lionsarmor/KeychainKreatures/PCBWay/05_Delivery_and_Testing/Inspection_Reports/README.md

# Save received inspection/test reports here

No test result is prefilled. Retain PCBWay net-test/inspection records and your own dated measurements with board serial numbers. Distinguish factory inspection, bare-board continuity and actual powered functional testing.
