lionsarmor/KeychainKreatures/PCBWay/01_Main_C6/01_Gerber_Upload/README.md

# Upload main C.6 Gerbers

Upload **UPLOAD_MAIN_C6_GERBERS.zip** to the MAIN bare-PCB job.

Quantity 5; 96 × 105 mm; 1.6 mm; **2 copper layers**. Read FABRICATION_REQUIREMENTS.md. Gerbers, outline, separate plated/non-plated drills and IPC netlist are included. Main is THT: omitted empty paste layers are intentional, and no assembly/stencil is requested.

Do not upload the power ZIP here. Confirm actual-size fit sheets and real modules before authorizing fabrication; the shell concept art is not fit evidence.
