lionsarmor/KeychainKreatures/PCBWay/01_Main_C6/02_Drawings_and_Reference/README.md

# Main reference drawings

These assembly, schematic and actual-size fit PDFs help PCBWay review the board and help you check purchased parts. They do **not** request factory assembly.

Print fit sheets at 100% and measure their calibration marks. Front and back illustrations have different viewing conventions. Use pad numbers for polarity, not guessed visual left/right order.
