lionsarmor/KeychainKreatures/PCBWay/01_Main_C6/05_Full_Review_Package/README.md

# Supplemental full main engineering package

Attach FULL_MAIN_C6_REVIEW.zip if the reviewer requests complete supporting CAD, datasheets or static checks. It is the existing issued ZIP, unchanged. For the fabrication upload use the smaller ZIP in ../01_Gerber_Upload instead.
