lionsarmor/KeychainKreatures/PCBWay/02_Power_P4/05_Full_Review_Package/README.md

# Supplemental full power engineering package

Attach FULL_POWER_P4_REVIEW.zip to engineering correspondence. It includes source CAD, datasheets, Gerbers, original BOMs/positions and saved electrical/routing checks. It is the issued ZIP, unchanged.

Upload the smaller Gerber ZIP, BOM and SMT centroid into their respective form fields. Do not treat this supplemental ZIP as another five-board order. Read the separate fabrication requirements before approving production.
