lionsarmor/KeychainKreatures/PCBWay/04_Approval_and_Payment/Receipts_and_Approvals/README.md

# Save approval and purchase records here

Currently empty of approvals/orders. Save final quote, explicit approvals, order IDs and receipts after you personally approve an order. Do not store payment credentials or identity documents. Files placed here are locally ignored by Git except this README.
