lionsarmor/KeychainKreatures/revisions/2026-09-12_current_only/KK_main_module/C5_relayout/manufacturing/DRILL_REPORT.txt

Drill report for KK_main_module.kicad_pcb
Created on 2026-09-11T15:05:44

Copper Layer Stackup:
    =============================================================
    L1 :  F.Cu                      front
    L2 :  B.Cu                      back

Drill file 'KK_main_module-PTH.drl' contains
    plated through holes:
    =============================================================
    T1  0.300mm  0.0118"  (40 holes))
    T2  0.400mm  0.0157"  (6 holes))
    T3  0.500mm  0.0197"  (3 holes))
    T4  0.750mm  0.0295"  (4 holes))
    T5  0.800mm  0.0315"  (201 holes))
    T6  0.900mm  0.0354"  (36 holes))
    T7  0.950mm  0.0374"  (4 holes))
    T8  1.000mm  0.0394"  (54 holes))
    T9  1.050mm  0.0413"  (18 holes))
    T10  1.100mm  0.0433"  (5 holes))

    Total plated holes count 371

Drill file 'KK_main_module-NPTH.drl' contains
    unplated through holes:
    =============================================================
    T1  2.200mm  0.0866"  (4 holes))

    Total unplated holes count 4
