lionsarmor/KeychainKreatures/revisions/2026-09-11_cleanup/KK_power_module/manufacturing/release/KK_power_module_0.2-LR1/drill_report.txt

Drill report for KK_power_module.kicad_pcb
Created on 2026-09-09T22:40:37

Copper Layer Stackup:
    =============================================================
    L1 :  F.Cu                      front
    L2 :  B.Cu                      back

Drill file 'KK_power_module-PTH.drl' contains
    plated through holes:
    =============================================================
    T1  0.300mm  0.0118"  (47 holes))
    T2  0.600mm  0.0236"  (4 holes)  (with 4 slots)
    T3  0.750mm  0.0295"  (4 holes))
    T4  1.000mm  0.0394"  (9 holes))

    Total plated holes count 64

Drill file 'KK_power_module-NPTH.drl' contains
    unplated through holes:
    =============================================================
    T1  0.650mm  0.0256"  (2 holes))
    T2  0.900mm  0.0354"  (2 holes))
    T3  2.200mm  0.0866"  (2 holes))

    Total unplated holes count 6
