lionsarmor/KeychainKreatures/revisions/2026-09-12_current_only/KK_main_module/mechanical/fit-study.pdf

# RODDY.WORLD / KEYCHAIN KREATURES

### FIT STUDY · 2026-09-10 · NOT A FABRICATION DRAWING

Print at 100% / actual size. Disable “fit to page”. Confirm the 20 mm calibration line below.

### FRONT · 1:1

62 mm · ring excluded

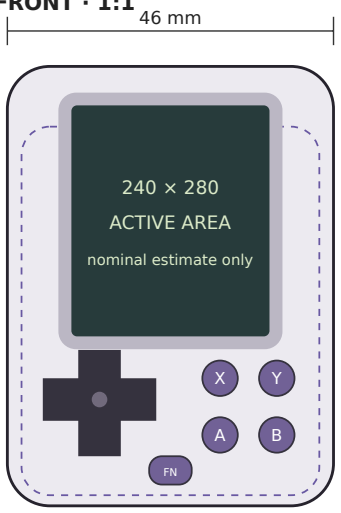
[picture p3: figure]
ACTIVE AREA; nominal estimate only
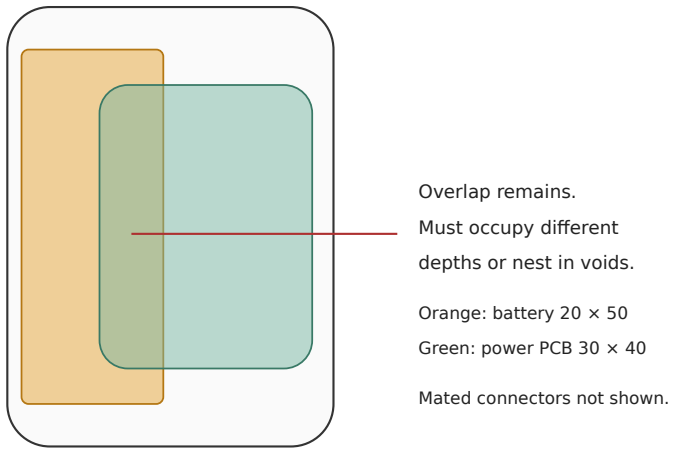
[picture p4: figure]
Overlap remains.; Must occupy different; depths or nest in voids.; Orange: battery 20 × 50; Green: power PCB 30 × 40; Mated connectors not shown.

Dashed: trial 42 × 52 mm PCB, R4. Caps/bezel/PCB position are illustrative. Glass, flex, bosses and travel NOT fitted.

### 19 mm DEPTH BUDGET · 4:1 diagram

Arithmetic lower bound at a four-assembly overlap.

10 mm cell

Gray: two 1.2 mm trial face skins = 2.4 mm

Green: two 1.6 mm PCB laminates = 3.2 mm

Red: ONLY 3.4 mm left for everything else

Display, parts, solder, insulation and gaps omitted.

This is not a physical layer-order drawing.

### OFFSET PLAN · 1:1 envelopes, NOT fitted

20 mm calibration

No screen reduction or housing growth approved.
