lionsarmor/KeychainKreatures/docs/enclosure_concepts/pixel_pod_round2/05_pixel_pod_snap_skins.png

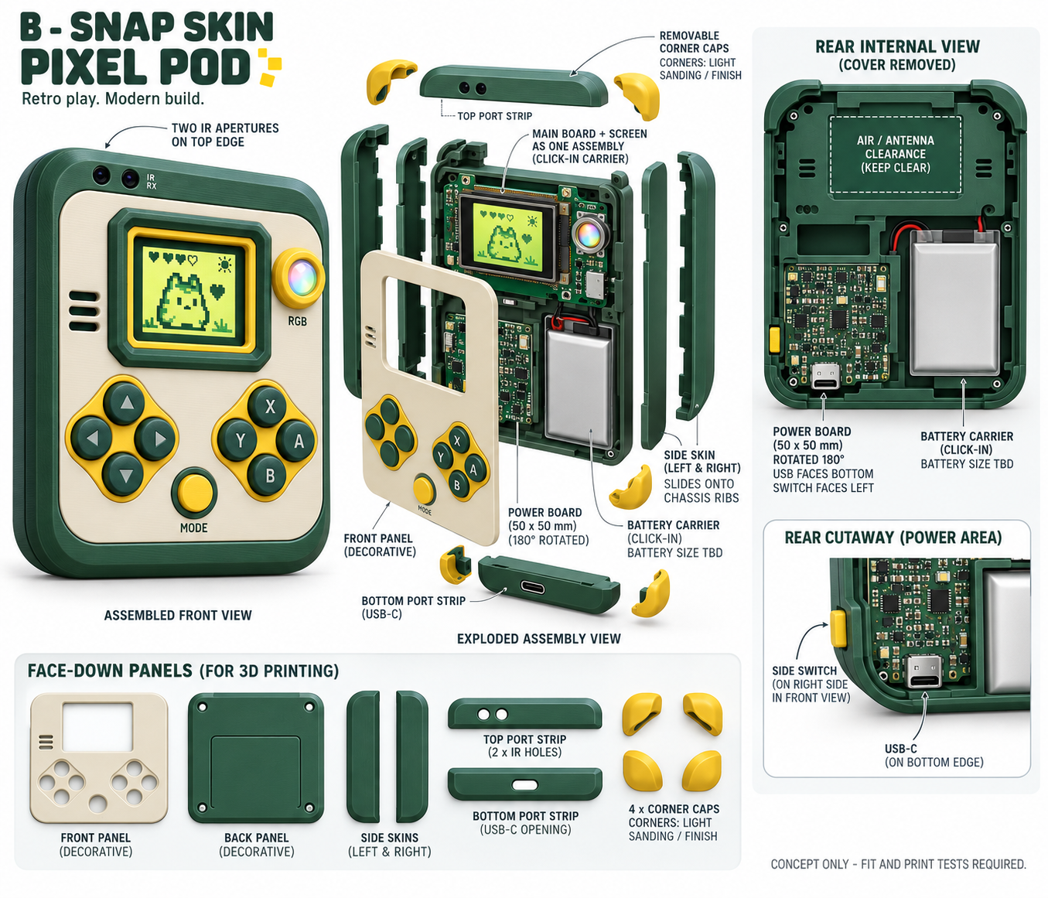
docs/enclosure_concepts/pixel_pod_round2/05_pixel_pod_snap_skins.png
