lionsarmor/KeychainKreatures/KK_main_module/datasheets/soft-buttons.png

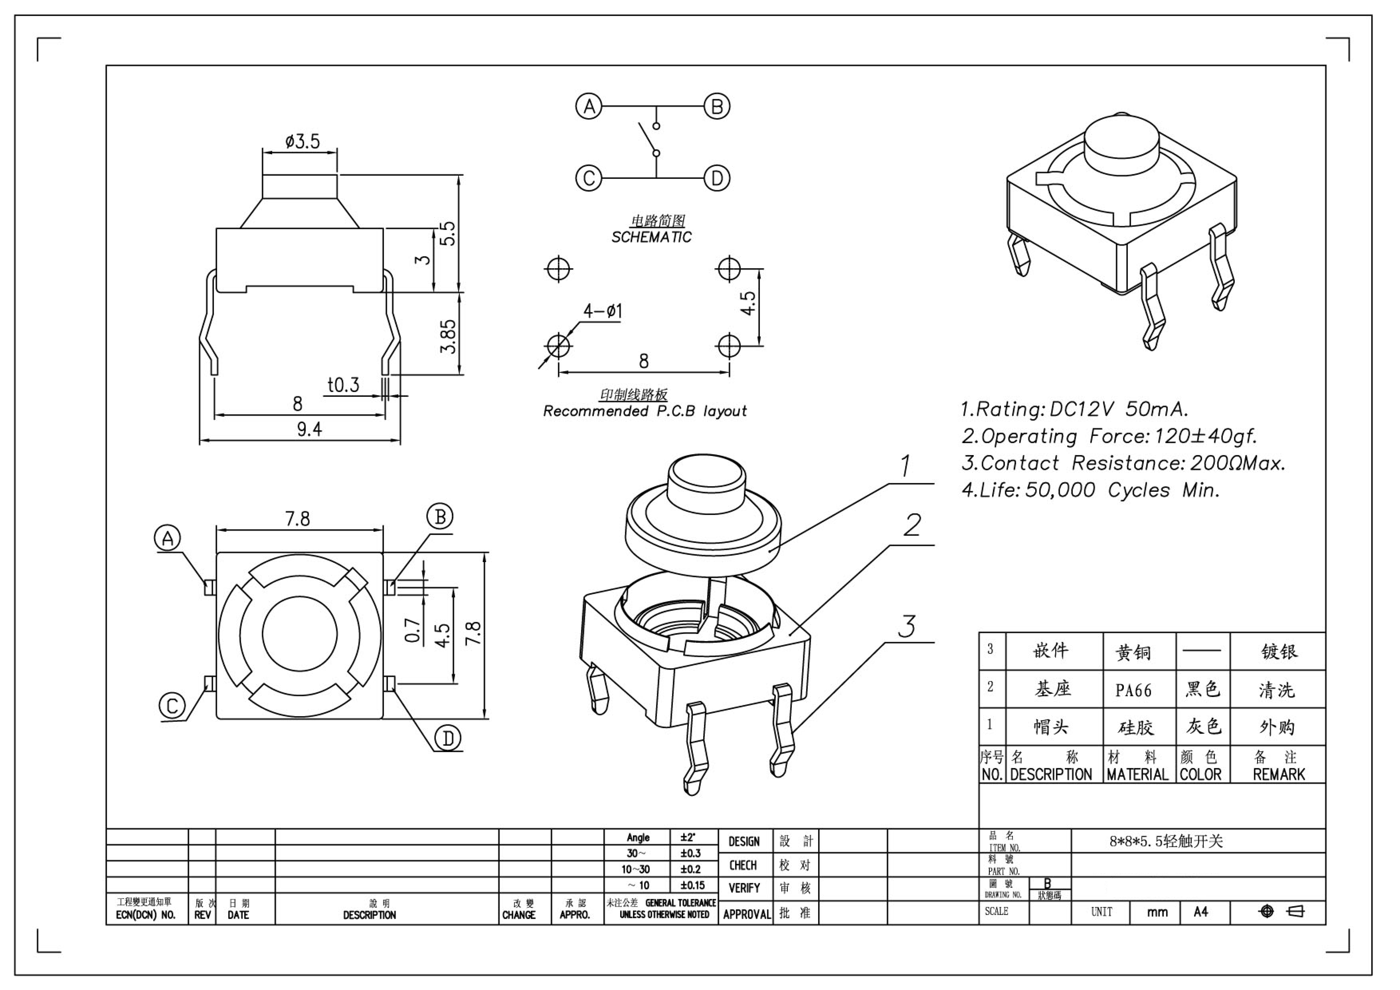
KK_main_module/datasheets/soft-buttons.png
