lionsarmor/KeychainKreatures/KK_power_module/datasheets/FS8205-pinout.png

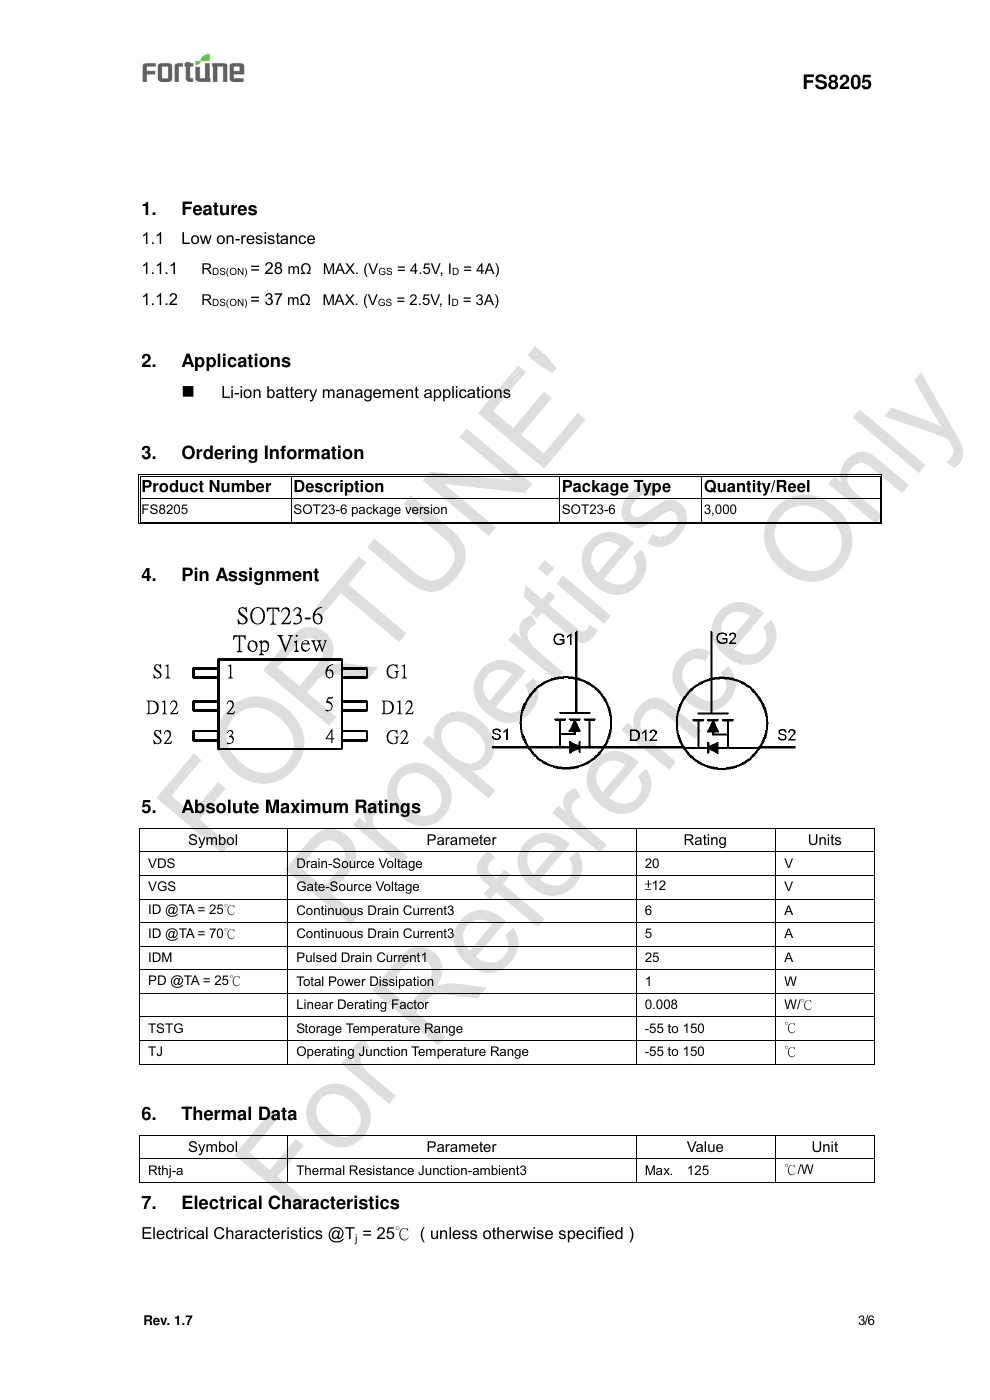
KK_power_module/datasheets/FS8205-pinout.png
