lionsarmor/KeychainKreatures/KK_power_module/datasheets/JST_VH-header.png

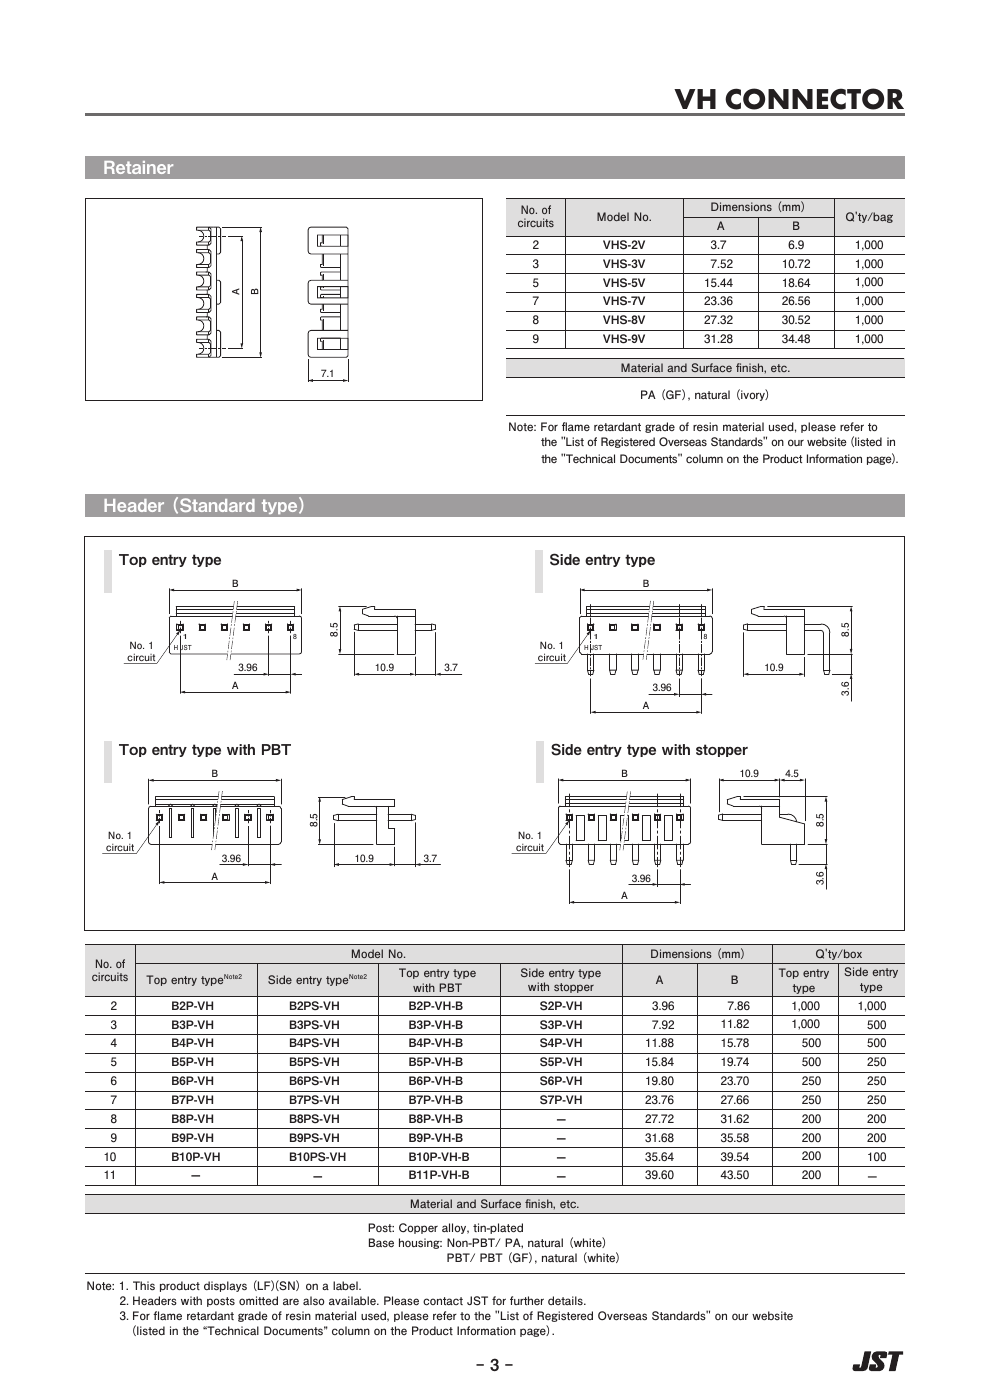
KK_power_module/datasheets/JST_VH-header.png
