lionsarmor/KeychainKreatures/KK_power_module/datasheets/USB-drawing.png

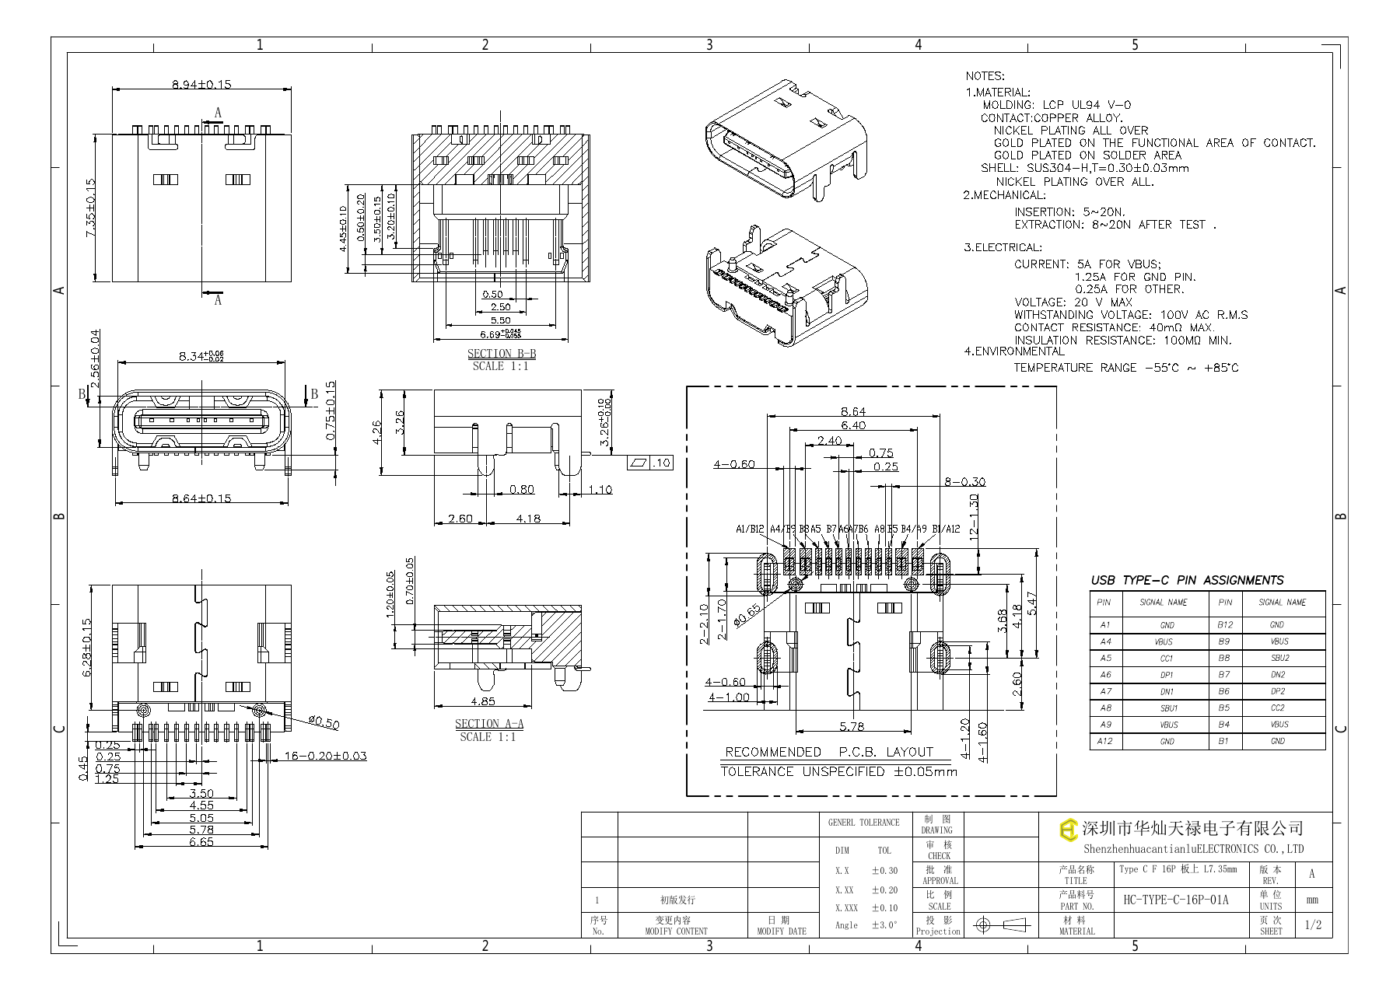
KK_power_module/datasheets/USB-drawing.png
