lionsarmor/KeychainKreatures/KK_power_module/P3_matching_stack/reports/power_front.png

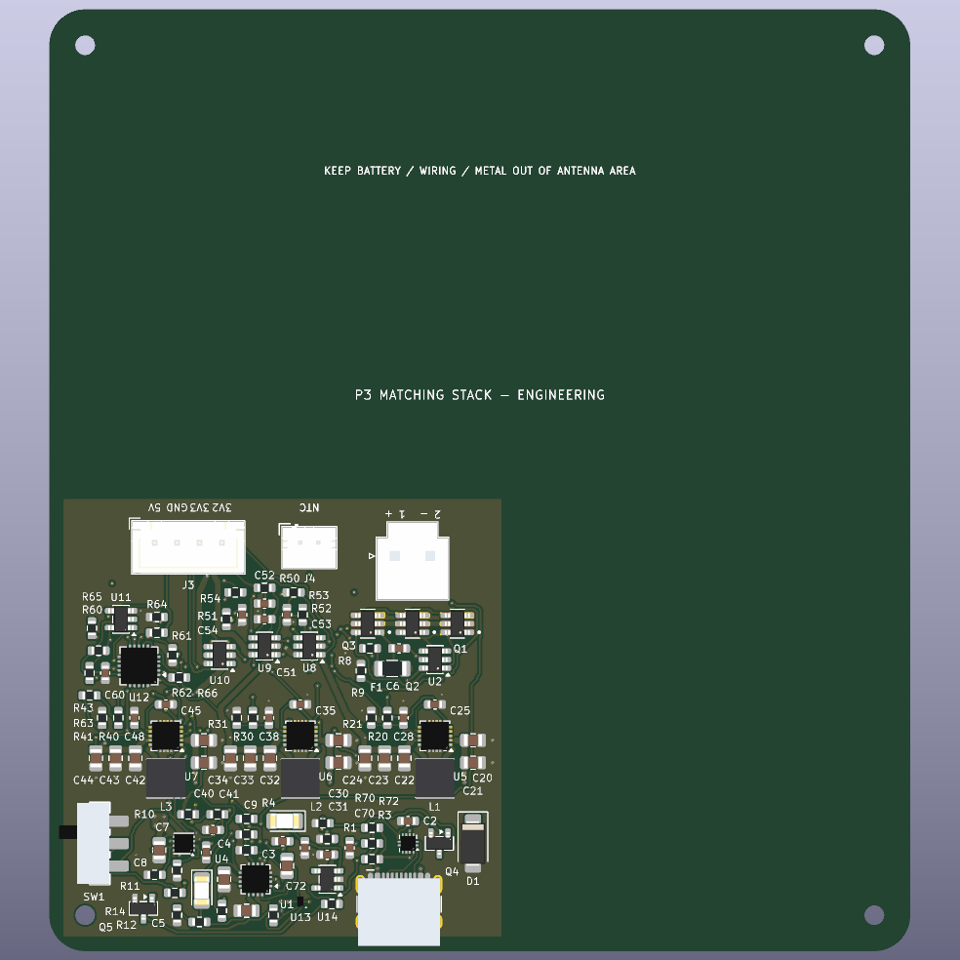
KK_power_module/P3_matching_stack/reports/power_front.png
