lionsarmor/KeychainKreatures/PCBWay/01_Main_C6/02_Drawings_and_Reference/main_oblique.png

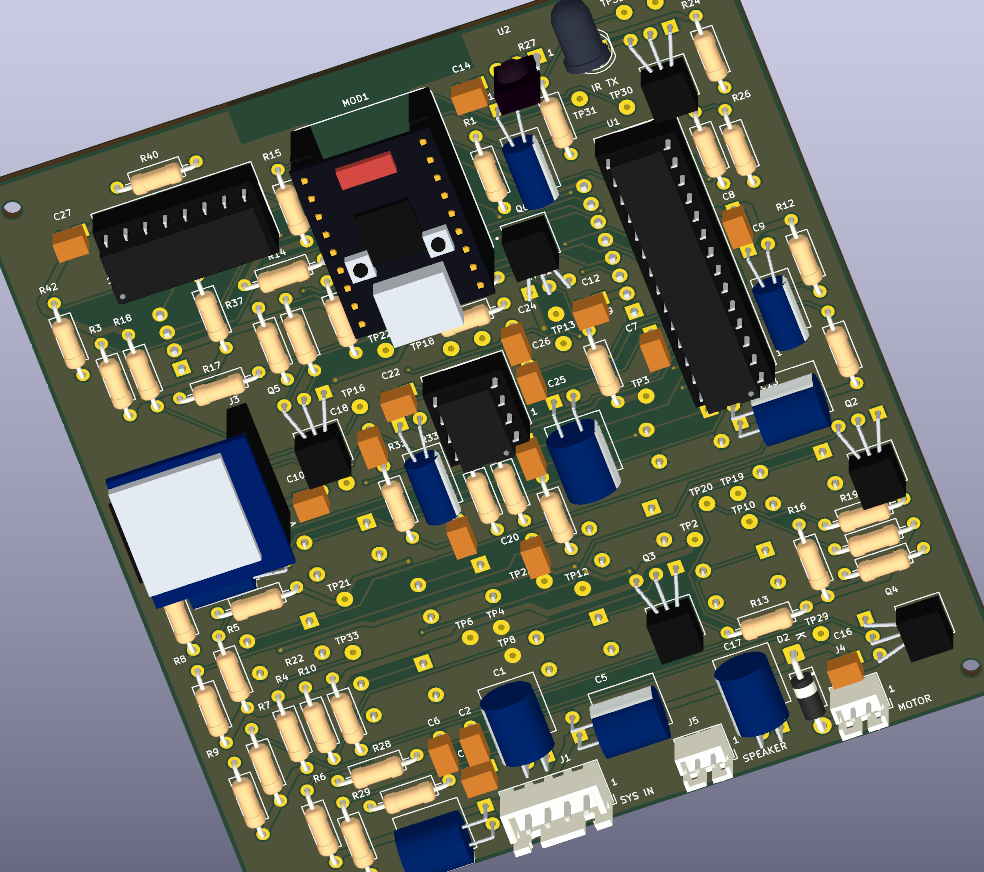
PCBWay/01_Main_C6/02_Drawings_and_Reference/main_oblique.png
