lionsarmor/KeychainKreatures/revisions/2026-09-11_cleanup/KK_power_module/P1_revision/schematic-preview.png

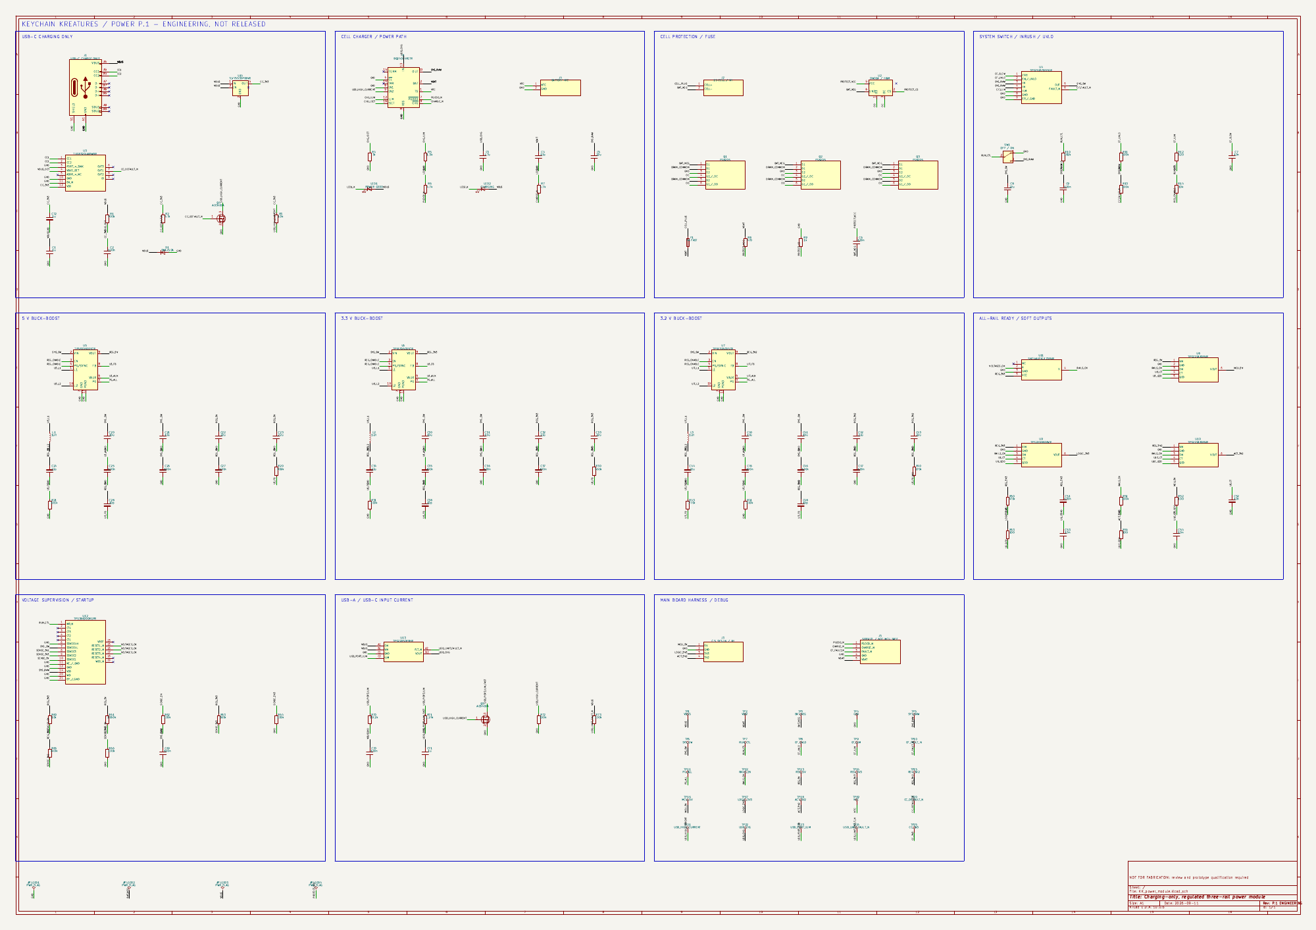
revisions/2026-09-11_cleanup/KK_power_module/P1_revision/schematic-preview.png
