lionsarmor/KeychainKreatures/PCBWay/03_Factory_DFM_and_Questions/Supplier_Responses/README.md

# Save PCBWay responses here

No supplier response has been received or invented. Save original quotes, DFM questions, CAM previews, sourcing proposals and inspection agreements here, retaining their dates and order/job IDs. Record accepted decisions in the adjacent checklist.
