lionsarmor/KeychainKreatures/revisions/2026-09-12_C6_P3_release/KK_main_module/manufacturing/ORDER_HOLD_FLAT_STACK.md

# Do not order these C.5 Gerbers for the revised toy

The user requested horizontal resistors, low-profile through-hole capacitors and matching stacked boards. C.6/P.3 are new 96 × 105 mm engineering candidates. Existing fabrication ZIPs in this directory have not been regenerated for those changes.

See `../../START_HERE.md` and `../../docs/FLAT_STACK_REWORK.md`. Print and check `../../docs/C6_P3_STACK_REVIEW.pdf`. Retain the old ZIPs for recovery only; do not treat them as the new stack's release.
