lionsarmor/KeychainKreatures/revisions/2026-09-12_C6_P3_release/KK_power_module/manufacturing/ORDER_HOLD_MATCHING_STACK.md

# Do not order these P.2 Gerbers for the revised toy

P.2 is the older 50 × 50 mm power board. The matching-stack P.3 candidate is **96 × 105 mm** with a new common mounting pattern. Existing fabrication/review ZIPs in this directory have not been regenerated for that change.

See `../../START_HERE.md` and `../../docs/FLAT_STACK_REWORK.md`. Retain old ZIPs for recovery only. P.3 still needs physical stack/connector/wire clearance review and a new manufacturing release.
