lionsarmor/KeychainKreatures/revisions/2026-09-12_current_only/KK_main_module/component_review/source_evidence/sd-dimensions.jpg

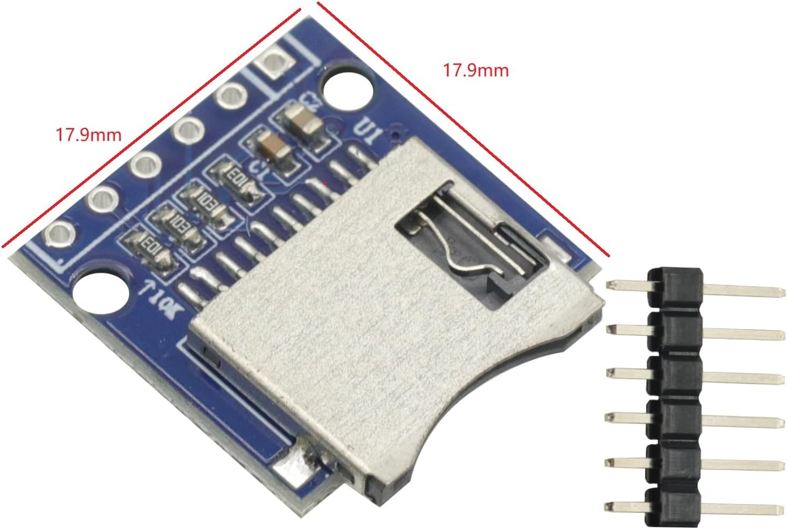
revisions/2026-09-12_current_only/KK_main_module/component_review/source_evidence/sd-dimensions.jpg
