lionsarmor/KeychainKreatures/PCBWay/01_Main_C6/03_Assembly_NOT_ORDERED/README.md

# Main assembly is NOT ordered

Order five BARE main PCBs only. Main parts, sockets, modules, buttons, harness and student assembly remain separate.

The full main review ZIP contains reference BOM/placement data for later use. Do not submit that BOM as an additional assembly job unless you intentionally change this scope. No main stencil or programming file is required for the proposed order.
