lionsarmor/KeychainKreatures/PCBWay/02_Power_P4/04_Assembly_Drawings/README.md

# Attach assembly references

Provide the schematic PDF, assembly/body PDFs, component-side render, connector pin map and assembly guide here. Front-side fitted positions total 108; rear bare test pads, mounting holes and silkscreen logo footprints are not fitted components.

All drawings are references, not proof of delivered-part fit. Bottom views are mirrored for viewing from the back. Use component drawings, pad-1 markers and designators to resolve polarity.

The power board requires factory SMT assembly and connector secondary operations, not student assembly. Keep all substitutions and orientation questions on hold for written approval.
