lionsarmor/KeychainKreatures/revisions/2026-09-12_current_only/KK_main_module/assembly/README.md

# Historical C.5 assembly packet — superseded

These files describe the older board, including upright-resistor instructions. They are retained as source history, **not current assembly directions**.

Use [C.6 assembly/wiring](../C6_flat_stack/assembly/ASSEMBLY_GUIDE.md), [current BOM](../C6_flat_stack/assembly/C6_BOM_BY_REFERENCE.csv), [paired-kit extras](../C6_flat_stack/assembly/C6_COMPLETE_KIT_EXTRAS.csv) and [current fit sheet](../../docs/C6_P3_STACK_REVIEW.pdf). Main C.6 and power P.3 share a 96 × 105 mm outline.
