lionsarmor/KeychainKreatures/revisions/2026-09-12_current_only/KK_power_module/work/P2_logo_review/prototype_package/TEST_PAD_GUIDE.md

# Test-pad guide — rear side

28 bare 1.5 mm probe pads; not fitted pins. Coordinates are front-view KiCad mm (Y down). The rear assembly drawing is mirrored for rear viewing.

**TP4 is GND. TP3 is BAT_NEG, not an interchangeable ground. Never bridge the protection return with grounded test equipment.**

| Pad | Signal | CAD X | CAD Y |
|---|---|---:|---:|
| TP1 | VBUS | 5.0 | 29.0 |
| TP2 | VBAT | 8.5 | 29.0 |
| TP3 | BAT_NEG | 12.0 | 29.0 |
| TP4 | GND | 15.8 | 28.5 |
| TP5 | SYS_RAW | 20.0 | 29.0 |
| TP6 | SYS_SW | 23.0 | 29.0 |
| TP7 | RUN_CTL | 26.5 | 29.0 |
| TP8 | EF_UVLO | 30.0 | 29.0 |
| TP9 | EF_ILIM | 34.0 | 29.0 |
| TP10 | EF_FAULT_N | 44.0 | 40.0 |
| TP11 | PG_ALL | 41.0 | 29.0 |
| TP12 | RAILS_EN | 44.5 | 29.0 |
| TP13 | REG_5V | 5.0 | 32.5 |
| TP14 | REG_3V3 | 8.5 | 32.5 |
| TP15 | REG_3V2 | 12.0 | 32.5 |
| TP16 | MCU_5V | 16.0 | 32.5 |
| TP17 | LOGIC_3V3 | 19.5 | 32.5 |
| TP18 | ACT_3V2 | 29.0 | 47.0 |
| TP19 | NTC | 22.0 | 41.0 |
| TP20 | CC_DEFAULT_N | 30.0 | 32.5 |
| TP21 | USB_HIGH_CURRENT | 34.0 | 32.5 |
| TP22 | USB_CHG | 37.5 | 32.5 |
| TP23 | USB_PORT_ILIM | 41.0 | 32.5 |
| TP24 | USB_LIMIT_FAULT_N | 44.5 | 32.5 |
| TP25 | CC_3V3 | 5.0 | 39.0 |
| TP26 | PGOOD_N | 8.0 | 39.0 |
| TP27 | CHARGE_N | 14.0 | 39.0 |
| TP28 | VOLTAGES_OK | 17.0 | 39.0 |
