lionsarmor/KeychainKreatures/revisions/2026-09-12_power_compact/P3_previous/KK_main_module/manufacturing/README.md

# Current C6 prototype outputs

- [KK_MAIN_C6_5_PROTOTYPE_REVIEW_2026-09-12.zip](KK_MAIN_C6_5_PROTOTYPE_REVIEW_2026-09-12.zip): complete five-sample review, CAD, BOM/placement, assembly/test guides, models, datasheets and checks.
- [KK_MAIN_C6_GERBERS.zip](KK_MAIN_C6_GERBERS.zip): Gerbers, drills, maps, IPC-D-356 and fabrication requirements.
- [KK_MAIN_C6_5_PROTOTYPE_REVIEW_2026-09-12/](KK_MAIN_C6_5_PROTOTYPE_REVIEW_2026-09-12/): unpacked matching review package.

Use C6 only with the paired C.6/P.3 revision. Both are 96 x 105 mm, but main has TWO copper layers and power FOUR. Factory DFM/component supply, physical fit and bench qualification remain required. Power needs filled/capped/planarized via-in-pad and fine-pitch WCSP assembly approval. Nothing ordered.

Superseded outputs moved to ../../revisions/2026-09-12_C6_P3_release/. Current hashes: ../../docs/C6_P3_RELEASE_INDEX.json. Do not manufacture the historical C.5/P.2 ZIPs.
