lionsarmor/KeychainKreatures/revisions/2026-09-11_cleanup/KK_main_module/pcb/backups/pre_c3_debug/assembly/README.md

# C.2 prototype assembly packet

C.2 engineering-prototype BOM. All 91 schematic positions are accounted for. J2/J3 already include their female sockets; do not buy them twice. Power module, battery and enclosure are outside this main-board release. Speaker rating, delivered module revisions and powered qualification remain release holds.

- [Print the complete BOM](C2_BOM_PRINT.html)
- [Grouped PCB purchasing BOM](C2_PCB_BOM.csv)
- [Every reference and its board side](C2_BOM_BY_REFERENCE.csv)
- [Sockets, modules, mating plugs and wiring](C2_KIT_EXTRAS.csv)
- [Assembly and bring-up guide](ASSEMBLY_GUIDE.md)

Older BOMs elsewhere in the project are historical and must not be combined with C.2. Optional bundled headers are not extra required purchases. Order at most a small engineering prototype batch before electrical tests.
