lionsarmor/KeychainKreatures/revisions/2026-09-11_cleanup/KK_main_module/pcb/backups/pre_c4_top_rgb/assembly/README.md

# C.3 RGB assembly packet

Use these files together for the 80 × 115 mm engineering prototype:

- [Printable complete BOM](C3_BOM_PRINT.html)
- [Grouped PCB purchasing BOM](C3_PCB_BOM.csv)
- [All 98 references, placement and datasheets](C3_BOM_BY_REFERENCE.csv)
- [Modules, sockets, mating plugs, wiring and hardware](C3_KIT_EXTRAS.csv)
- [Assembly, orientation, wiring and startup](ASSEMBLY_GUIDE.md)
- [25-point debug guide](C3_DEBUG_GUIDE.md)
- [Bench acceptance record — all tests initially pending](C3_BENCH_TEST_RECORD.csv)
- [26-document datasheet packet](C3_DATASHEETS.zip)

J2/J3 already count their female sockets: do not purchase them twice. D1 is IR, D3 is RGB. J4/J5 use B2B-PH top-entry parts, not historical S2B side-entry parts. U4 needs the added ED16DT socket. Bare TP holes remain unpopulated.

Power module, battery and enclosure are outside this main-board package. Speaker power rating, delivered module revisions, physical dry-fit and powered qualification remain open. Historical C.2 lists must not be mixed into this BOM.
