lionsarmor/KeychainKreatures/revisions/2026-09-12_power_compact/P3_previous/KK_main_module/manufacturing/KK_MAIN_C6_5_PROTOTYPE_REVIEW_2026-09-12/cad/README.md

# Current prototype project

This is the authoritative revised CAD directory. Open the .kicad_pro beside this README, not older root or archived CAD. Current BOM/assembly documents are in ../assembly/; fresh native checks and maps are in ../verification/. The project uses KiCad 10 and standard KiCad library models plus the supplied local libraries.

The project is a prototype only. See ../READ_FIRST.md for current manufacturing ZIPs, hashes, paired-board wiring and remaining factory, physical-fit and bench qualification requirements. Do not rerun old placement or routing scripts over this board.
