lionsarmor/KeychainKreatures/docs/enclosure_concepts/pixel_pod_round3/08_pixel_pod_simple_assembly.png

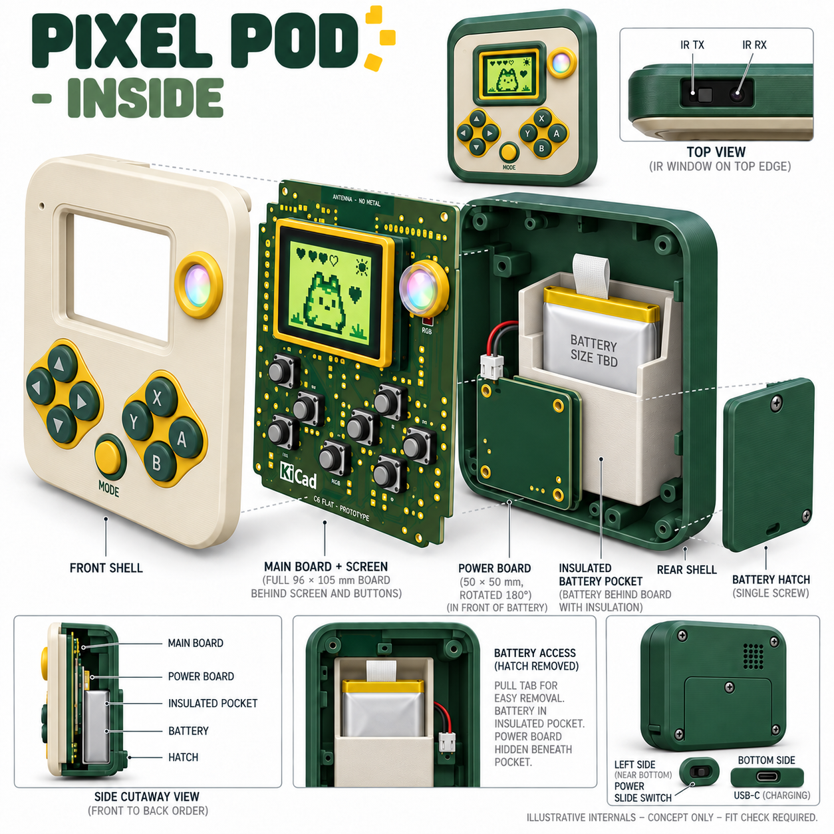
docs/enclosure_concepts/pixel_pod_round3/08_pixel_pod_simple_assembly.png
