lionsarmor/KeychainKreatures/PCBWay/02_Power_P4/04_Assembly_Drawings/power_front.png

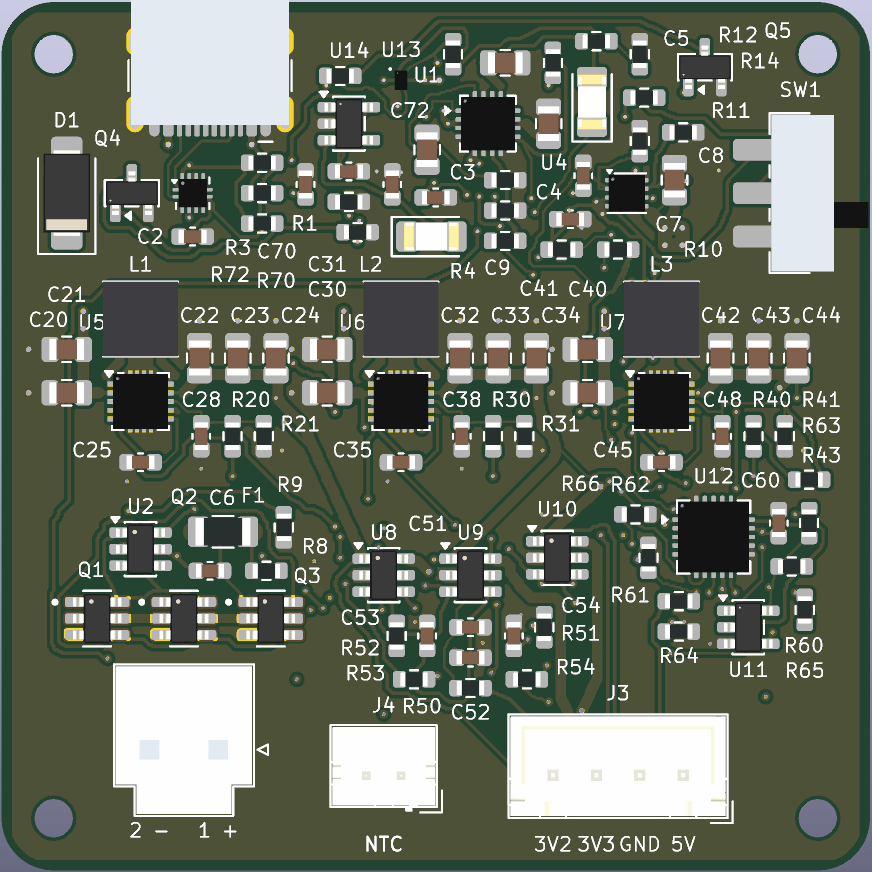
PCBWay/02_Power_P4/04_Assembly_Drawings/power_front.png
