lionsarmor/KeychainKreatures/revisions/2026-09-12_current_only/KK_main_module/component_review/VALIDATION.md

# Design-table validation — revision B

Generated by `node KK_main_module/component_review/build_design_tables.mjs`.

PASS: 84 BOM rows; 36 unique logical-circuit references; 107 pin/contact records; 17 resistors, 5 capacitors. Referenced local datasheet paths exist. All physical MCU GPIO/header assignments are explicitly withdrawn; MOD1 has logical ports only. MCP23017 has all 28 pins accounted for with GPA7/GPB7 unused. Every connected net has at least two endpoints. Battery, external VBUS and external 5 V nets are absent from the logical circuit. Deferred integrated-power rows have zero main-board quantity.

NOT CHECKED: SuperMini GPIO feasibility, physical module pin mapping, SYS_IN circuit, ERC, SPICE or hardware behavior. This is not a wireable main-board schematic. The previous Waveshare pin-map validation no longer applies. No KiCad schematic or PCB was generated.
