lionsarmor/KeychainKreatures/revisions/2026-09-12_current_only/KK_main_module/pcb/README.md

# Historical C.2–C.5 tools and drawings

Files in this folder are engineering history and helper dependencies, not current manufacturing sources. Do not run old placement or routing generators over the revised PCB.

Use [current C.6 project](../C6_flat_stack/KK_main_module.kicad_pro), [fresh checks](../C6_flat_stack/release_checks/), [actual-size front fit](../C6_flat_stack/assembly/C6_front_FIT_100_PERCENT.pdf), [back fit](../C6_flat_stack/assembly/C6_back_FIT_100_PERCENT.pdf) and [both project releases](../../START_HERE.md). The current shared outline is 96 × 105 mm, not older dimensions shown in this folder.
