lionsarmor/KeychainKreatures/KK_power_module/assembly/TROUBLESHOOTING_POWER_P4.html

Student/instructor engineering-prototype guide. Follow the safety gates; record unperformed tests as NOT RUN or BLOCKED.

# Power P.4 — troubleshooting and factory-return guide

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

## 1. What should a factory-delivered board do?

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

## 2. Stop conditions and prohibited shortcuts

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

## 3. The two returns: the most important wiring rule

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

## 4. Equipment and record keeping

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

## 5. P1 — unpowered incoming inspection

Check the 50 × 50 mm/R3 outline, four 2.2 mm mounting holes, intact board edges and P.4 revision. Inspect USB shell anchors, connector latches, switch and both copper faces. Look for missing components, wrong orientation, displaced tiny parts, solder beads, damaged pads or scratches. Use the reference BOM/placement (https://github.com/lionsarmor/KeychainKreatures/blob/52bfa1ec090cb6baee13dd3303d0df844ae71aad/KK_power_module/release_checks/BOM_AND_PLACEMENT.csv) and schematic (https://github.com/lionsarmor/KeychainKreatures/blob/52bfa1ec090cb6baee13dd3303d0df844ae71aad/KK_power_module/assembly/SCHEMATIC.pdf), not an older revision's coordinates.

The assembler must confirm these particularly important parts, not just that a package fits:

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

## 6. P2 — verify the connectors and fuse without power

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

## 7. Understand the stages before chasing an output

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

## 8. P3 — battery-simulator startup, USB disconnected

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

### Locate the first missing stage

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

## 9. P4 — qualify the outputs with no main attached

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

## 10. P5 — controlled loads and low-voltage behavior

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

## 11. P6 — USB input and current selection

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

## 12. P7 — charging and the temperature sensor

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

The nominal full charge-current setting is about 0.303 A, screened 0.271–0.332 A under the reviewed conditions. Precharge, near-full taper, thermal regulation, input limits or system load can legitimately lower it. Do not demand 0.303 A at every battery voltage. Verify termination and recharge behavior against BQ24075T's datasheet (https://github.com/lionsarmor/KeychainKreatures/blob/52bfa1ec090cb6baee13dd3303d0df844ae71aad/KK_power_module/datasheets/BQ24075TRGTR.pdf), recording source, battery voltage, temperature and load conditions.

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

## 13. P8 — reverse feed, sequencing and final integration

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

## 14. Quick symptom route

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

## 15. Complete test-point reference

All 28 test points are on B.Cu, the rear copper face. Coordinate values below are native front-view CAD coordinates, X right/Y down; rear drawings are mirrored. Use the reference label and assembly drawings (https://github.com/lionsarmor/KeychainKreatures/tree/52bfa1ec090cb6baee13dd3303d0df844ae71aad/KK_power_module/release_checks/drawings) to locate the actual pad. Attach clips with power off, support the board and do not bridge adjacent pads.

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

## 16. When to send it back instead of repairing it

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

Sources: P.4 electrical review (https://github.com/lionsarmor/KeychainKreatures/blob/52bfa1ec090cb6baee13dd3303d0df844ae71aad/KK_power_module/assembly/P4_REVIEW_AND_TEST.md), test-point map (https://github.com/lionsarmor/KeychainKreatures/blob/52bfa1ec090cb6baee13dd3303d0df844ae71aad/KK_power_module/release_checks/TEST_POINTS.csv), connector map (https://github.com/lionsarmor/KeychainKreatures/blob/52bfa1ec090cb6baee13dd3303d0df844ae71aad/KK_power_module/release_checks/CONNECTOR_PIN_MAP.csv), calculated screening (https://github.com/lionsarmor/KeychainKreatures/blob/52bfa1ec090cb6baee13dd3303d0df844ae71aad/KK_power_module/electrical_screening.json), DW01A (https://github.com/lionsarmor/KeychainKreatures/blob/52bfa1ec090cb6baee13dd3303d0df844ae71aad/KK_power_module/datasheets/DW01A.pdf), FS8205 (https://github.com/lionsarmor/KeychainKreatures/blob/52bfa1ec090cb6baee13dd3303d0df844ae71aad/KK_power_module/datasheets/FS8205_rev1_7.pdf), TPS259530 (https://github.com/lionsarmor/KeychainKreatures/blob/52bfa1ec090cb6baee13dd3303d0df844ae71aad/KK_power_module/datasheets/TPS259530DSGR.pdf), TPS63060 (https://github.com/lionsarmor/KeychainKreatures/blob/52bfa1ec090cb6baee13dd3303d0df844ae71aad/KK_power_module/datasheets/TPS63060DSCR.pdf), TPS386000 (https://github.com/lionsarmor/KeychainKreatures/blob/52bfa1ec090cb6baee13dd3303d0df844ae71aad/KK_power_module/datasheets/TPS386000RGPR.pdf), TPS22950 (https://github.com/lionsarmor/KeychainKreatures/blob/52bfa1ec090cb6baee13dd3303d0df844ae71aad/KK_power_module/datasheets/TPS22950YBHR.pdf), 103AT-2 (https://github.com/lionsarmor/KeychainKreatures/blob/52bfa1ec090cb6baee13dd3303d0df844ae71aad/KK_power_module/datasheets/103AT-2.pdf). This supplement does not alter CAD or previously issued manufacturing ZIPs.
