lionsarmor/KeychainKreatures/revisions/2026-09-12_current_only/docs/C6_P3_STACK_REVIEW-3.pdf

## Main-board rear - populated mechanical preview

C.6 / P.3 PROTOTYPE REVIEW - PHYSICAL / BENCH QUALIFICATION PENDING

Preview is not a powered test. Seller-module envelopes and formed leads need sample checks.

Use C6_flat_stack and P3_matching_stack, not the old manufacturing ZIPs.
