lionsarmor/KeychainKreatures/revisions/2026-09-11_cleanup/KK_main_module/pcb/c2-back-final.png

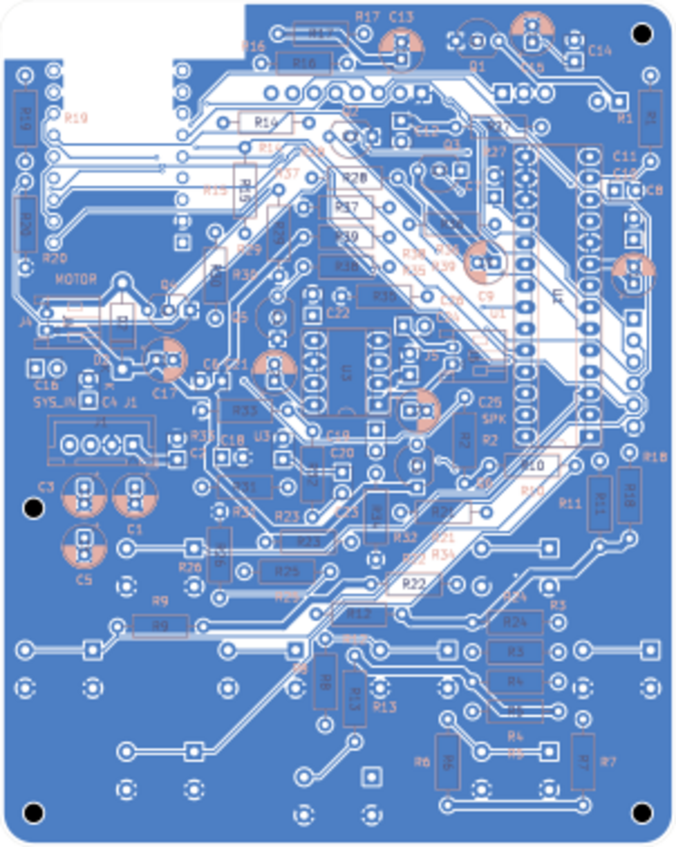
revisions/2026-09-11_cleanup/KK_main_module/pcb/c2-back-final.png
