lionsarmor/KeychainKreatures/revisions/2026-09-11_cleanup/KK_main_module/pcb/c2-back.png

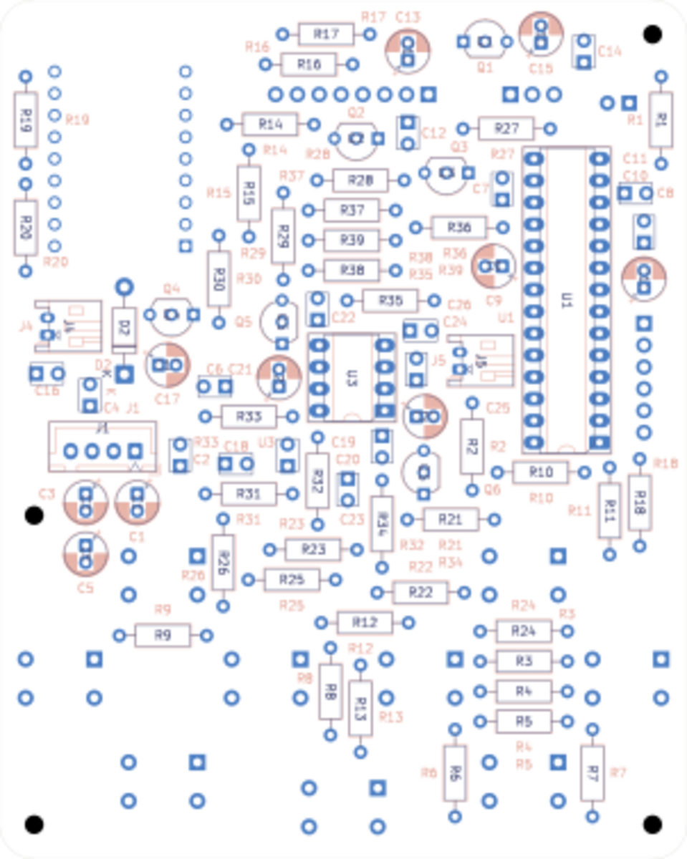
revisions/2026-09-11_cleanup/KK_main_module/pcb/c2-back.png
