lionsarmor/KeychainKreatures/revisions/2026-09-11_cleanup/KK_main_module/pcb/c3-back-3d.png

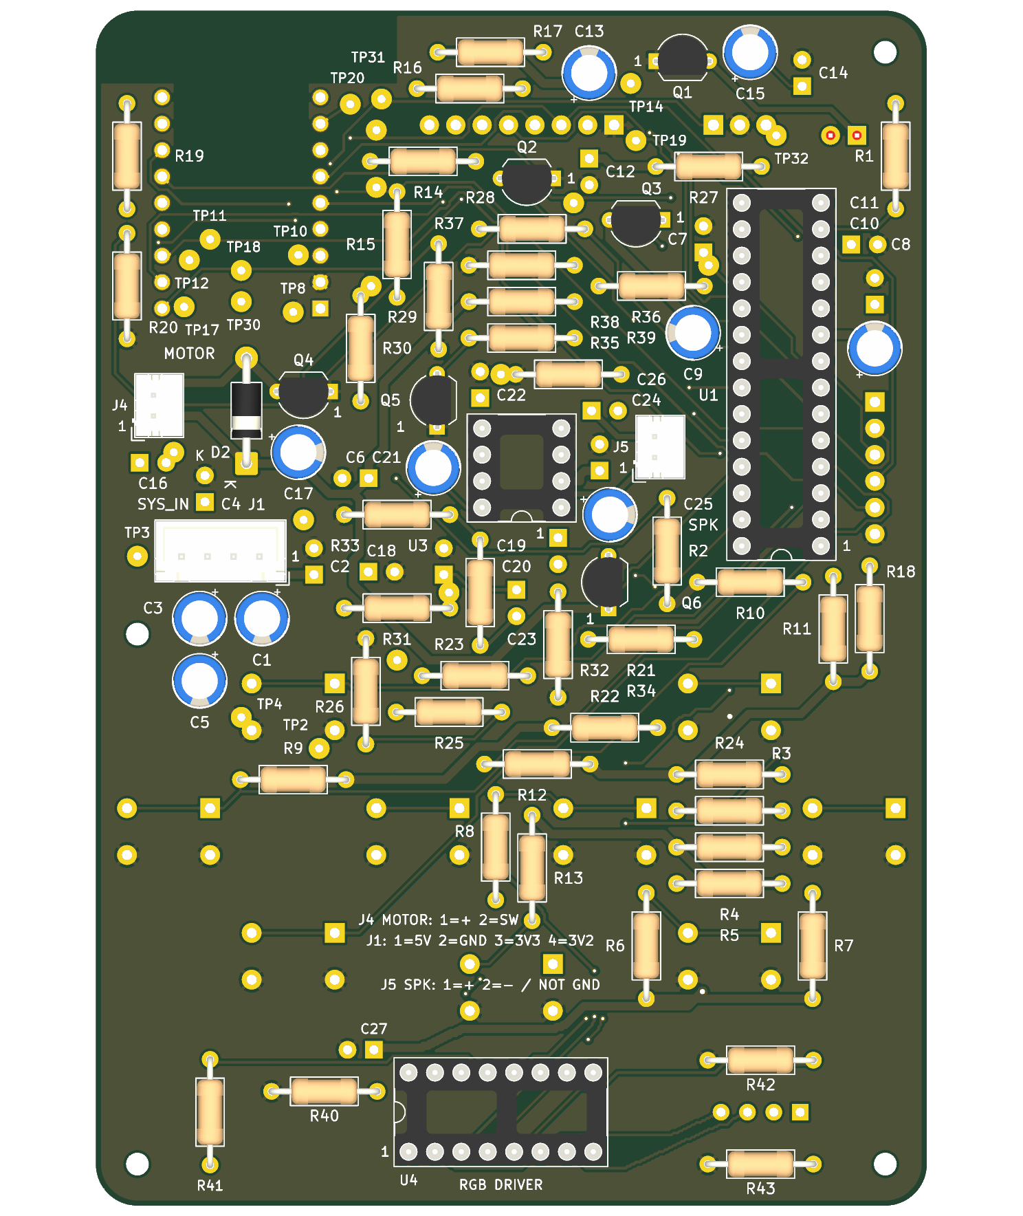
revisions/2026-09-11_cleanup/KK_main_module/pcb/c3-back-3d.png
