lionsarmor/KeychainKreatures/revisions/2026-09-12_current_only/KK_main_module/C5_relayout/angled-3d.png

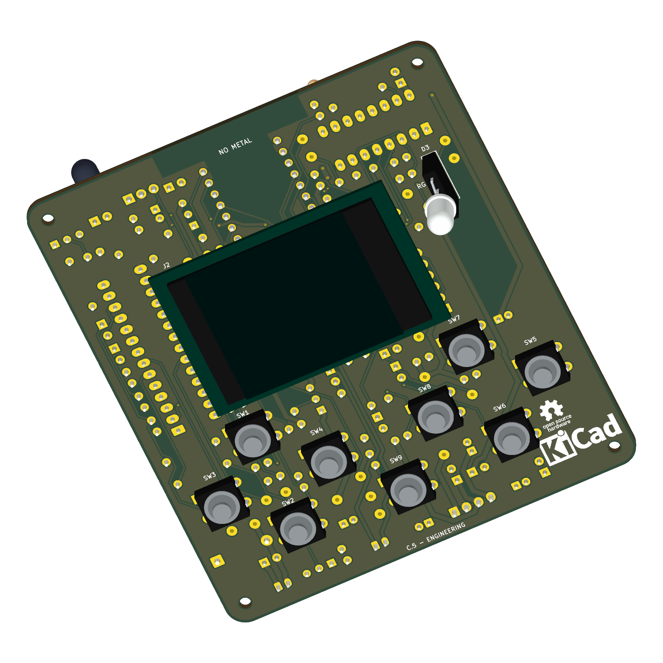
revisions/2026-09-12_current_only/KK_main_module/C5_relayout/angled-3d.png
