lionsarmor/KeychainKreatures/revisions/2026-09-12_current_only/KK_power_module/work/P2_review/inner1_review.png

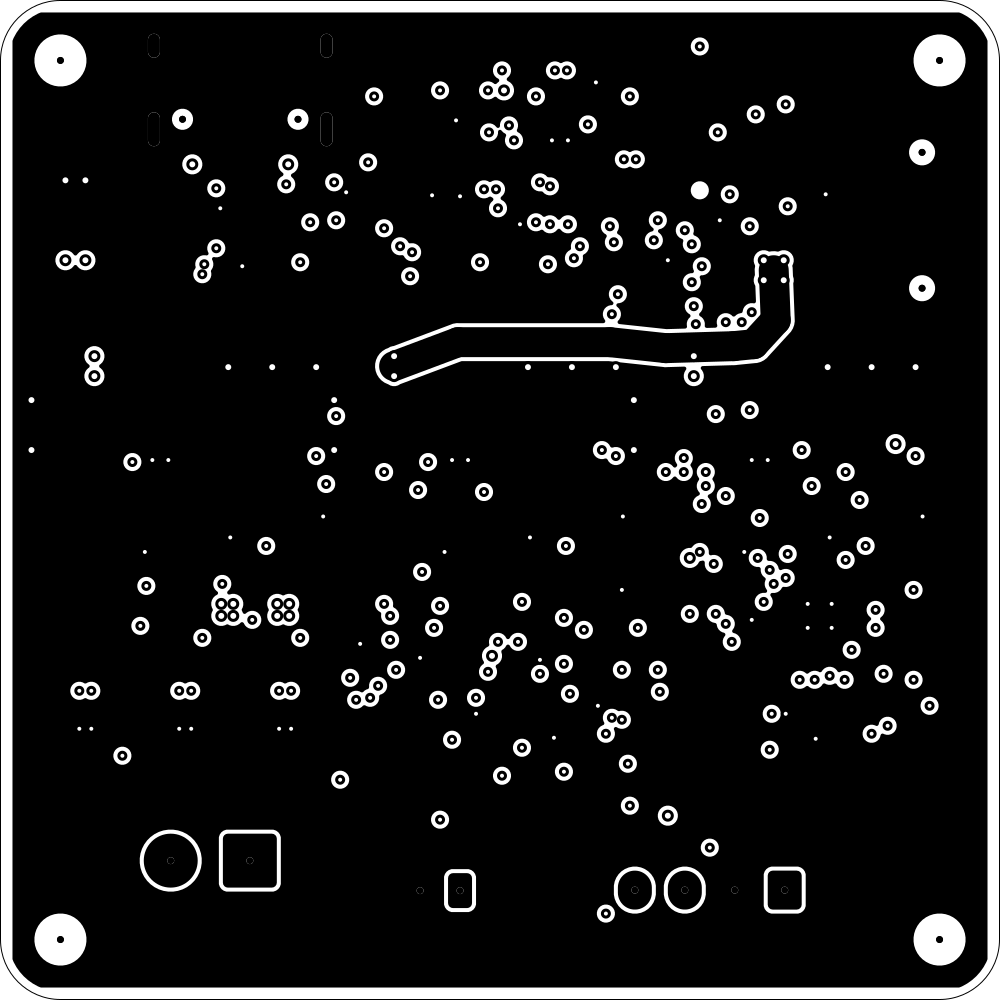
revisions/2026-09-12_current_only/KK_power_module/work/P2_review/inner1_review.png
