lionsarmor/KeychainKreatures/PCBWay/02_Power_P4/04_Assembly_Drawings/SCHEMATIC.pdf

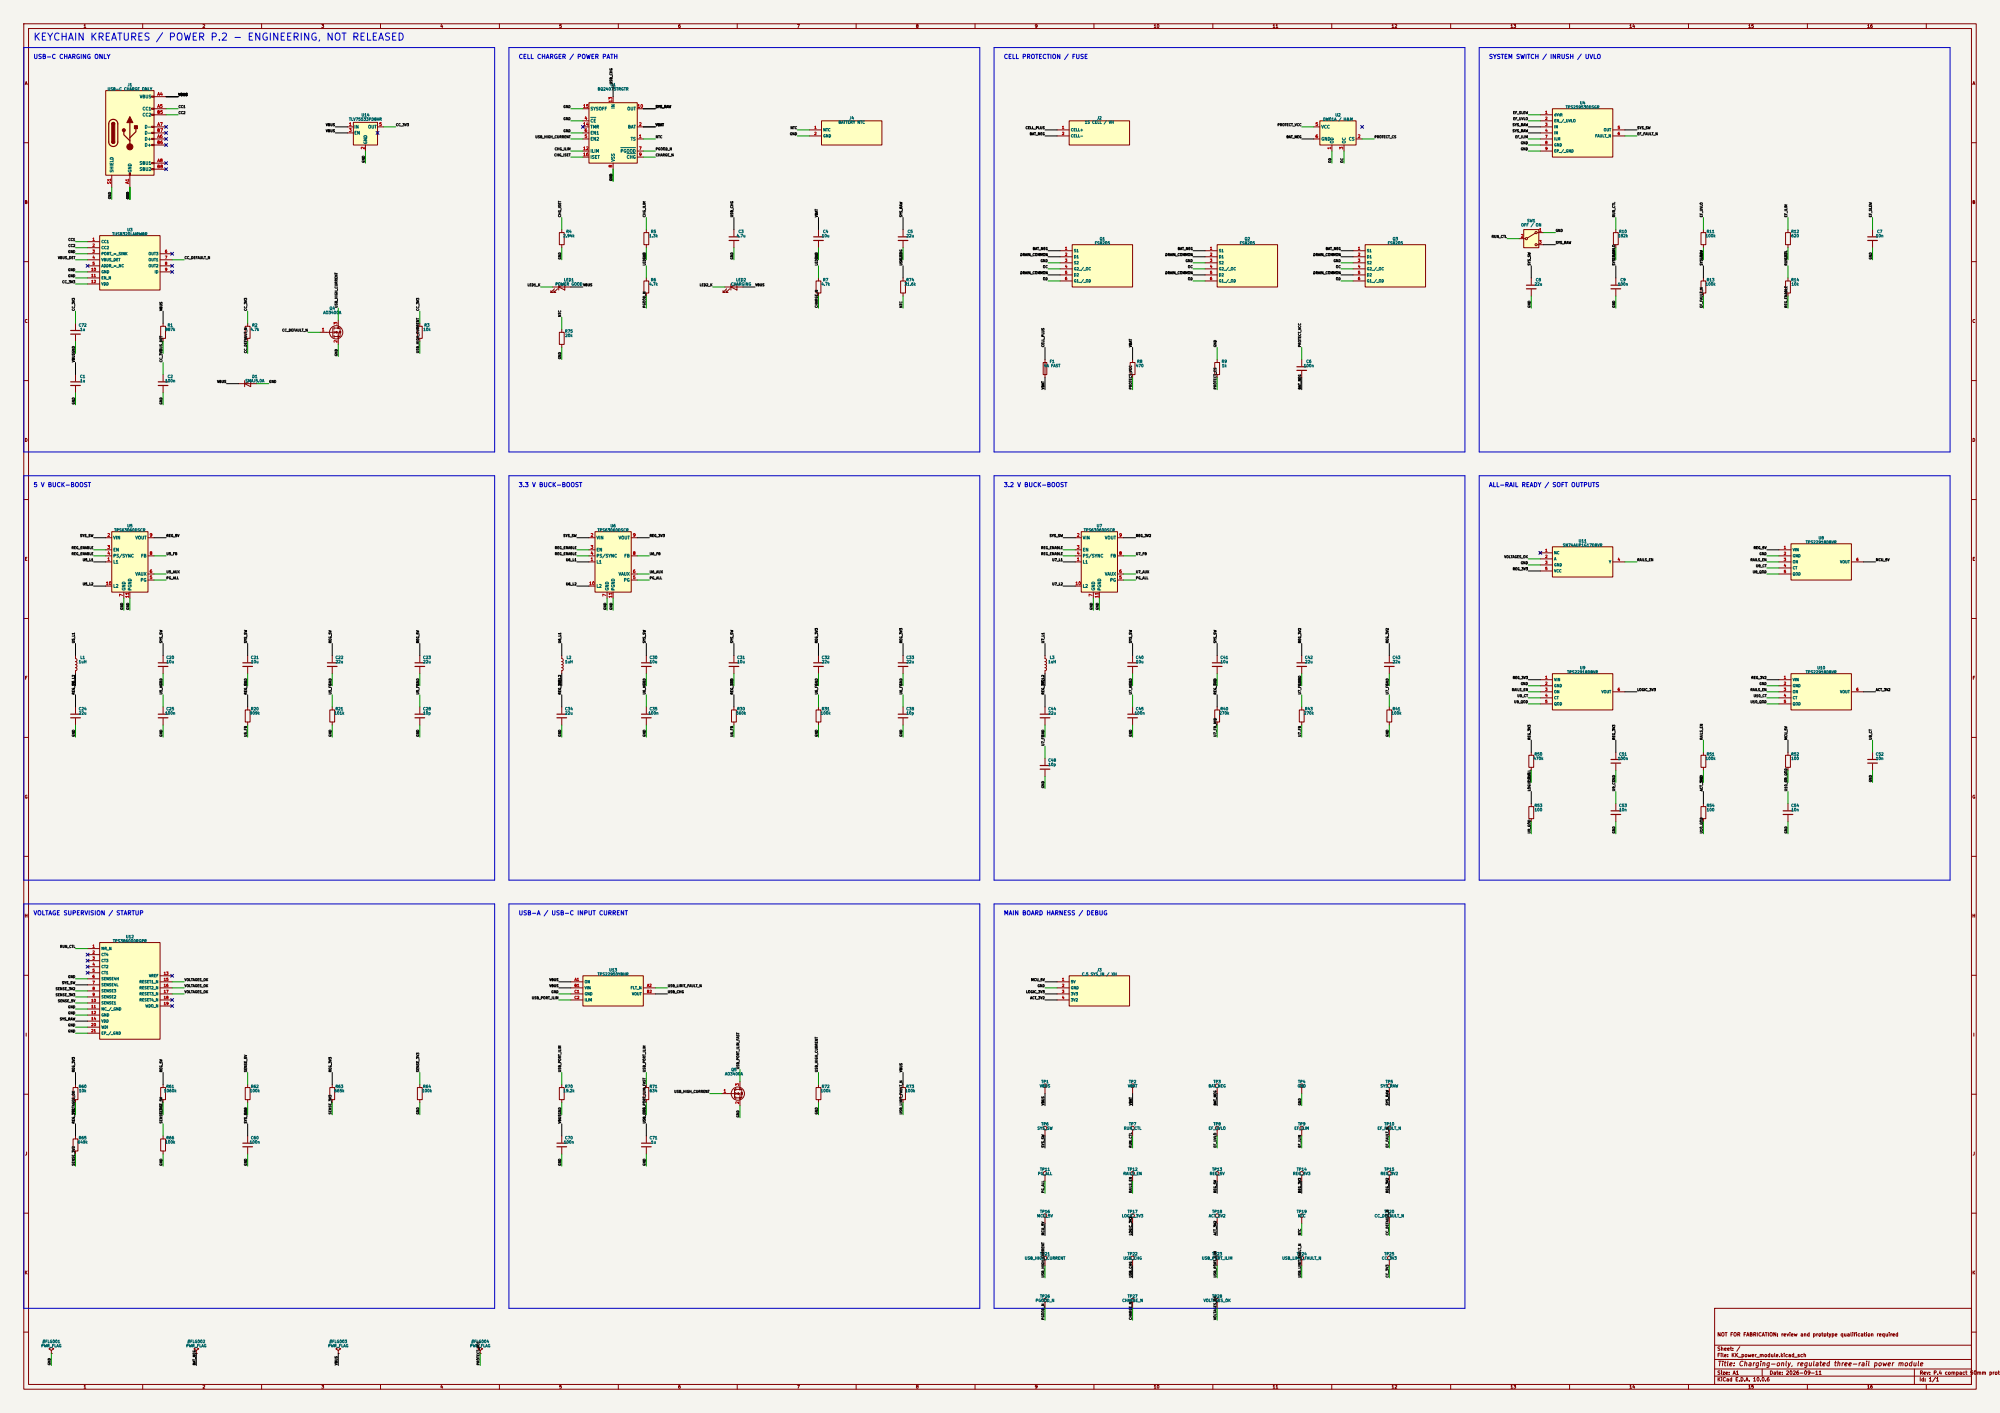
[picture p47: page 1]

KEYCHAIN KREATURES / POWER P.2 - ENGINEERING, NOT RELEASED

CELL CHARGER / POWER PATH

ALL-RAIL READY / SOFT OUTPUTS

MAIN BOARD HARNESS / DEBUG

NOT FOR FABRICATION: review and prototype qualification required

Sheet: /
File: KK_power_module.kicad_sch
Title: Charging-only, regulated three-rail power module
KiCad E.D.A. 10.0.6
