lionsarmor/KeychainKreatures/revisions/2026-09-12_C6_P3_release/desktop/PRINT_THIS_before_C6_P3.pdf

1 D3


A NO METAL KEYCHAIN KREATURES

LANDSCAPE 280 x 240 / SAMPLE FIT REQUIRED C.5 ENGINEERING PROTOTYPE - HARDWARE TESTS PENDING

# C8R2R4 C7 Q1D2

# J4 R39 R16 U1 R17 R26


K KK MAIN C.5 - REAR FIT CHECK / 84 x 95mm / PROTOTYPE
