lionsarmor/KeychainKreatures/revisions/2026-09-11_cleanup/KK_main_module/routing/C3_schematic_preview.pdf

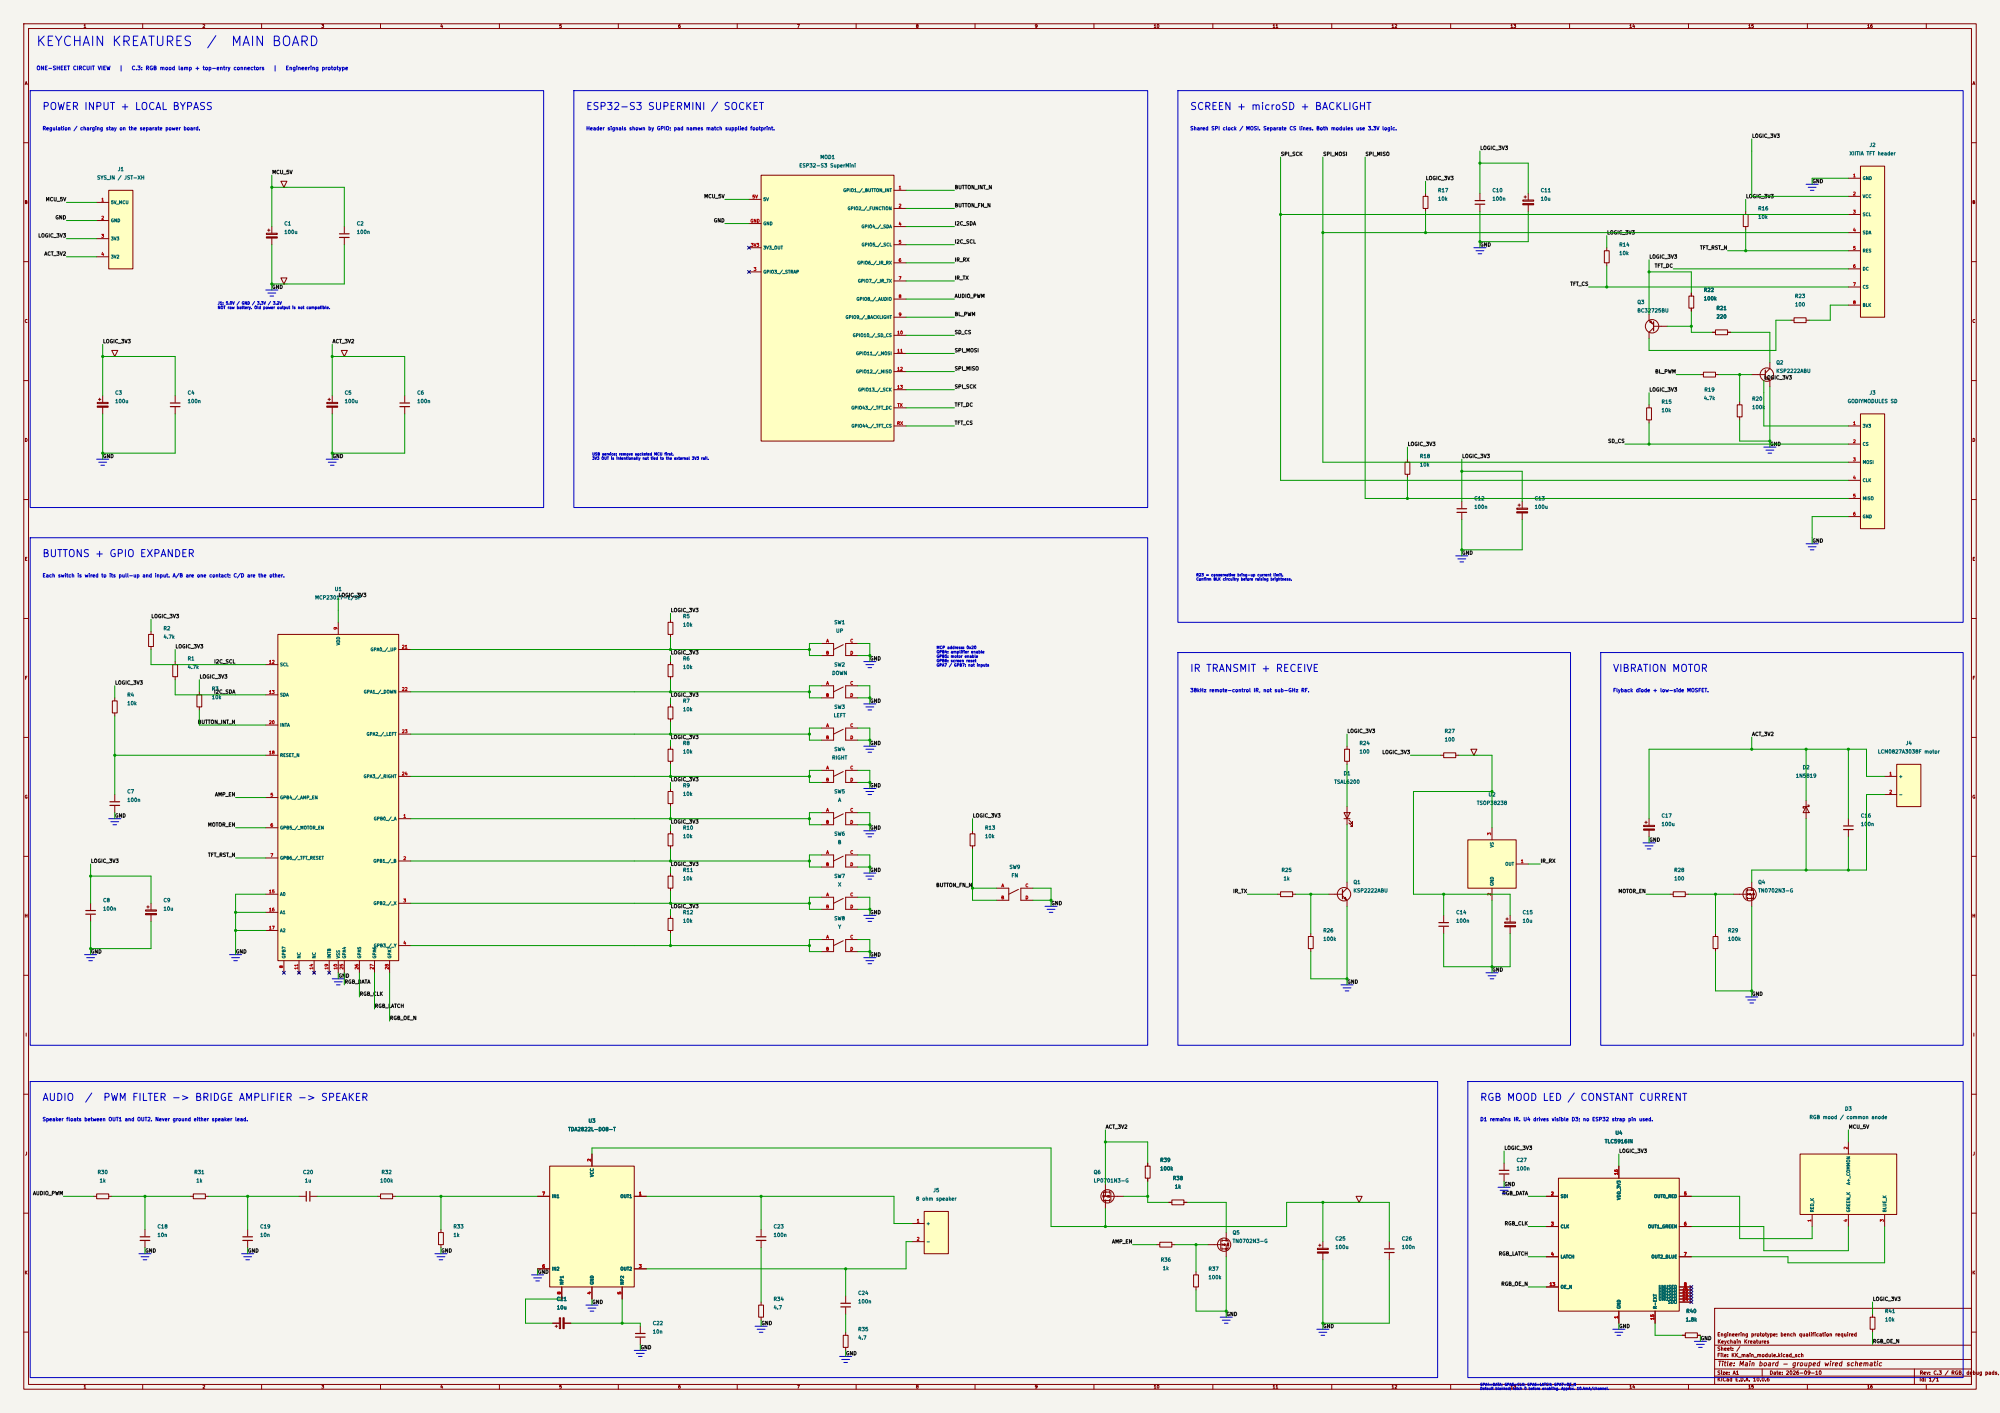
[picture p48: page 1]

KEYCHAIN KREATURES / MAIN BOARD

POWER INPUT + LOCAL BYPASS

Regulation / charging stay on the separate power board.

Header signals shown by GPIO; pad names match supplied footprint.

Shared SPI clock / MOSI. Separate CS lines. Both modules use 3.3V logic.

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

R23 = conservative bring-up current limit. Confirm BLK circuitry before raising brightness.

MCP address: 0x20 GPB4: amplifier enable GPB5: motor enable GPB6: screen reset GPA7 / GPB7: not inputs

38kHz remote-control IR, not sub-GHz RF.

Flyback diode + low-side MOSFET.

AUDIO / PWM FILTER -> BRIDGE AMPLIFIER -> SPEAKER

RGB MOOD LED / CONSTANT CURRENT
14 R-EXT 15 VDD_3V3 16

Speaker floats between OUT1 and OUT2. Never ground either speaker lead.

D1 remains IR. U4 drives visible D3; no ESP32 strap pin used.

RGB mood / common anode

Sheet: / File: KK_main_module.kicad_sch

Title: Main board - grouped wired schematic

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
