lionsarmor/KeychainKreatures/revisions/2026-09-11_cleanup/KK_main_module/schematic/KK_main_module.pdf

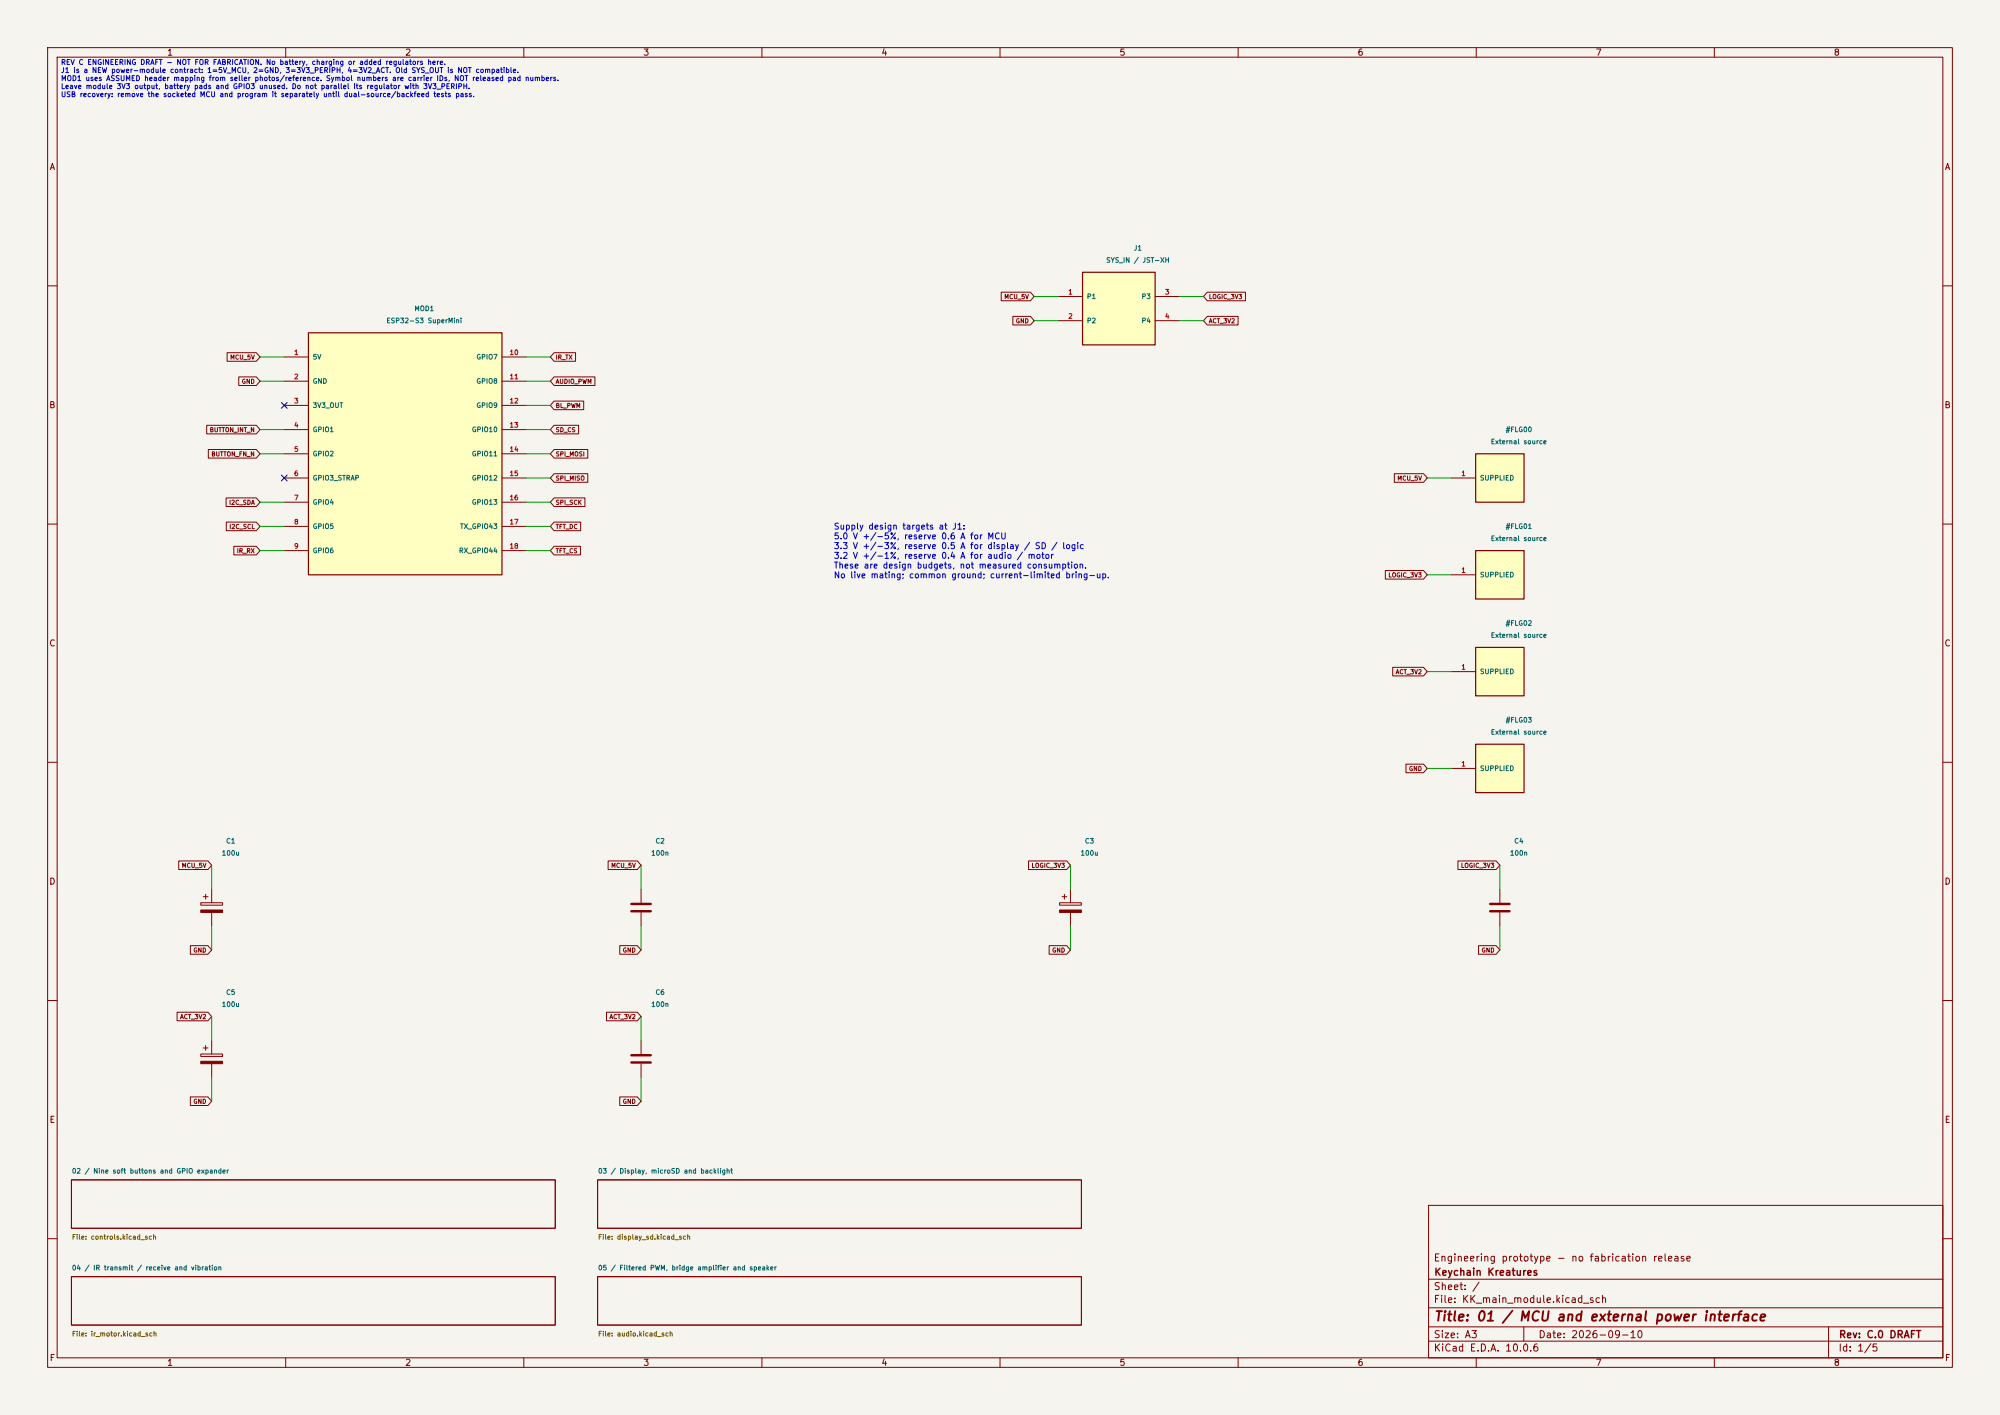
[picture p49: page 1]

3.3 V +/-3%, reserve 0.5 A for display / SD / logic 3.2 V +/-1%, reserve 0.4 A for audio / motor These are design budgets, not measured consumption. No live mating; common ground; current-limited bring-up.

05 / Filtered PWM, bridge amplifier and speaker File: audio.kicad_sch 03 / Display, microSD and backlight File: display_sd.kicad_sch 04 / IR transmit / receive and vibration

File: ir_motor.kicad_sch 02 / Nine soft buttons and GPIO expander File: controls.kicad_sch

Engineering prototype - no fabrication release
Keychain Kreatures
Sheet: /
File: KK_main_module.kicad_sch
Title: 01 / MCU and external power interface

Size: A3 | Rev: C.0 DRAFT | F Date: 2026-09-10
KiCad E.D.A. 10.0.6 | Id: 1/5

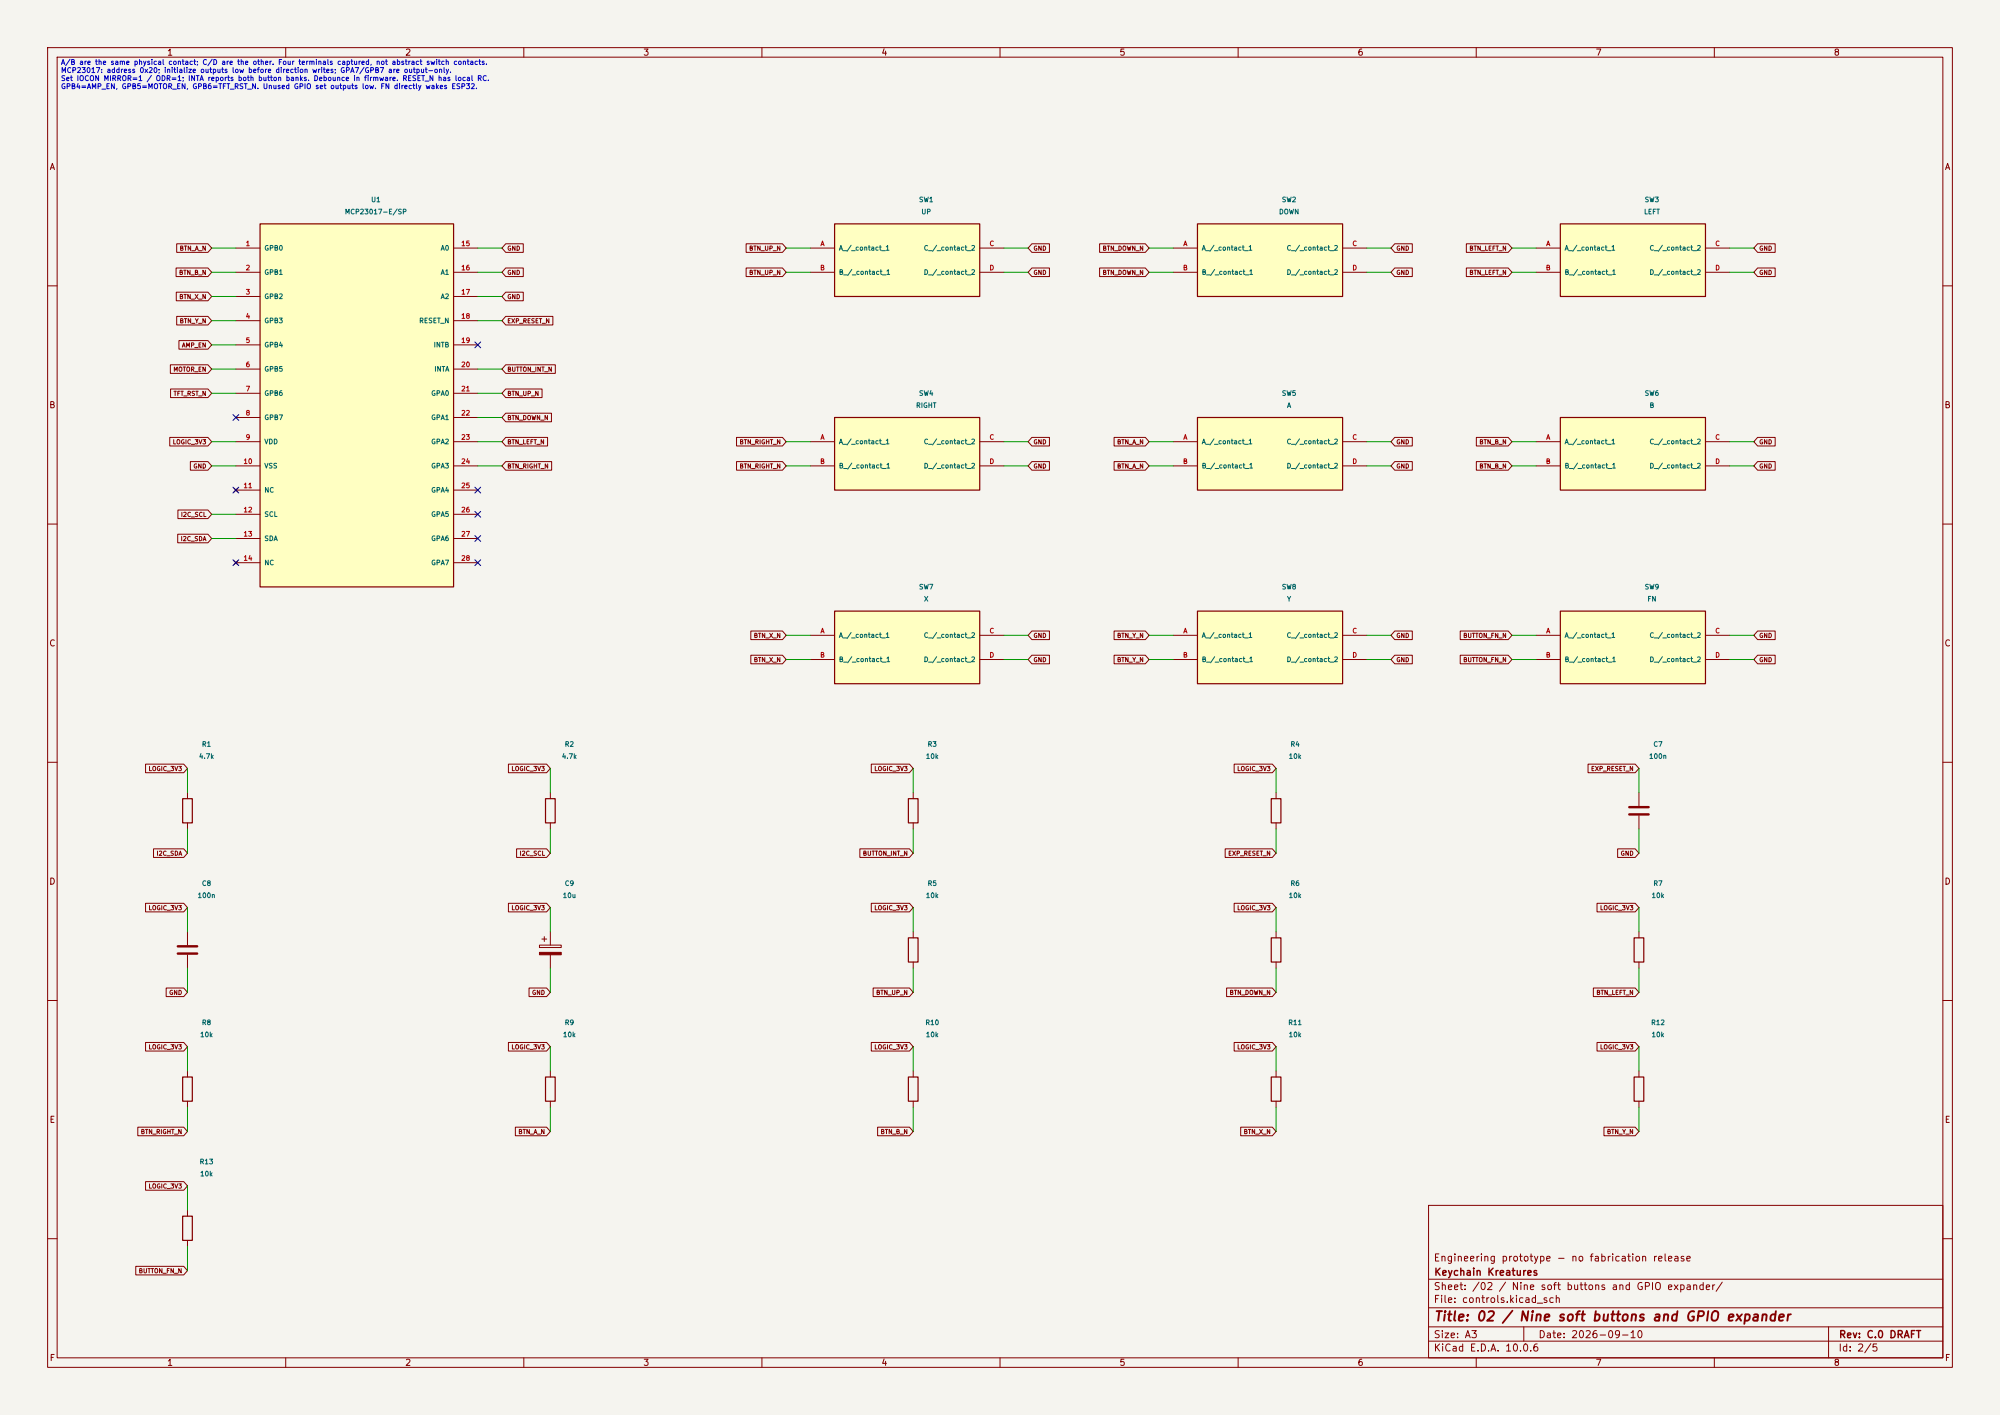
[picture p50: page 2]

A/B are the same physical contact; C/D are the other. Four terminals captured, not abstract switch contacts. MCP23017: address 0x20; initialize outputs low before direction writes; GPA7/GPB7 are output-only. Set IOCON MIRROR=1 / ODR=1; INTA reports both button banks. Debounce in firmware. RESET_N has local RC. GPB4=AMP_EN, GPB5=MOTOR_EN, GPB6=TFT_RST_N. Unused GPIO set outputs low. FN directly wakes ESP32.

Engineering prototype - no fabrication release
Keychain Kreatures
Sheet: /02 / Nine soft buttons and GPIO expander/
File: controls.kicad_sch
Title: 02 / Nine soft buttons and GPIO expander

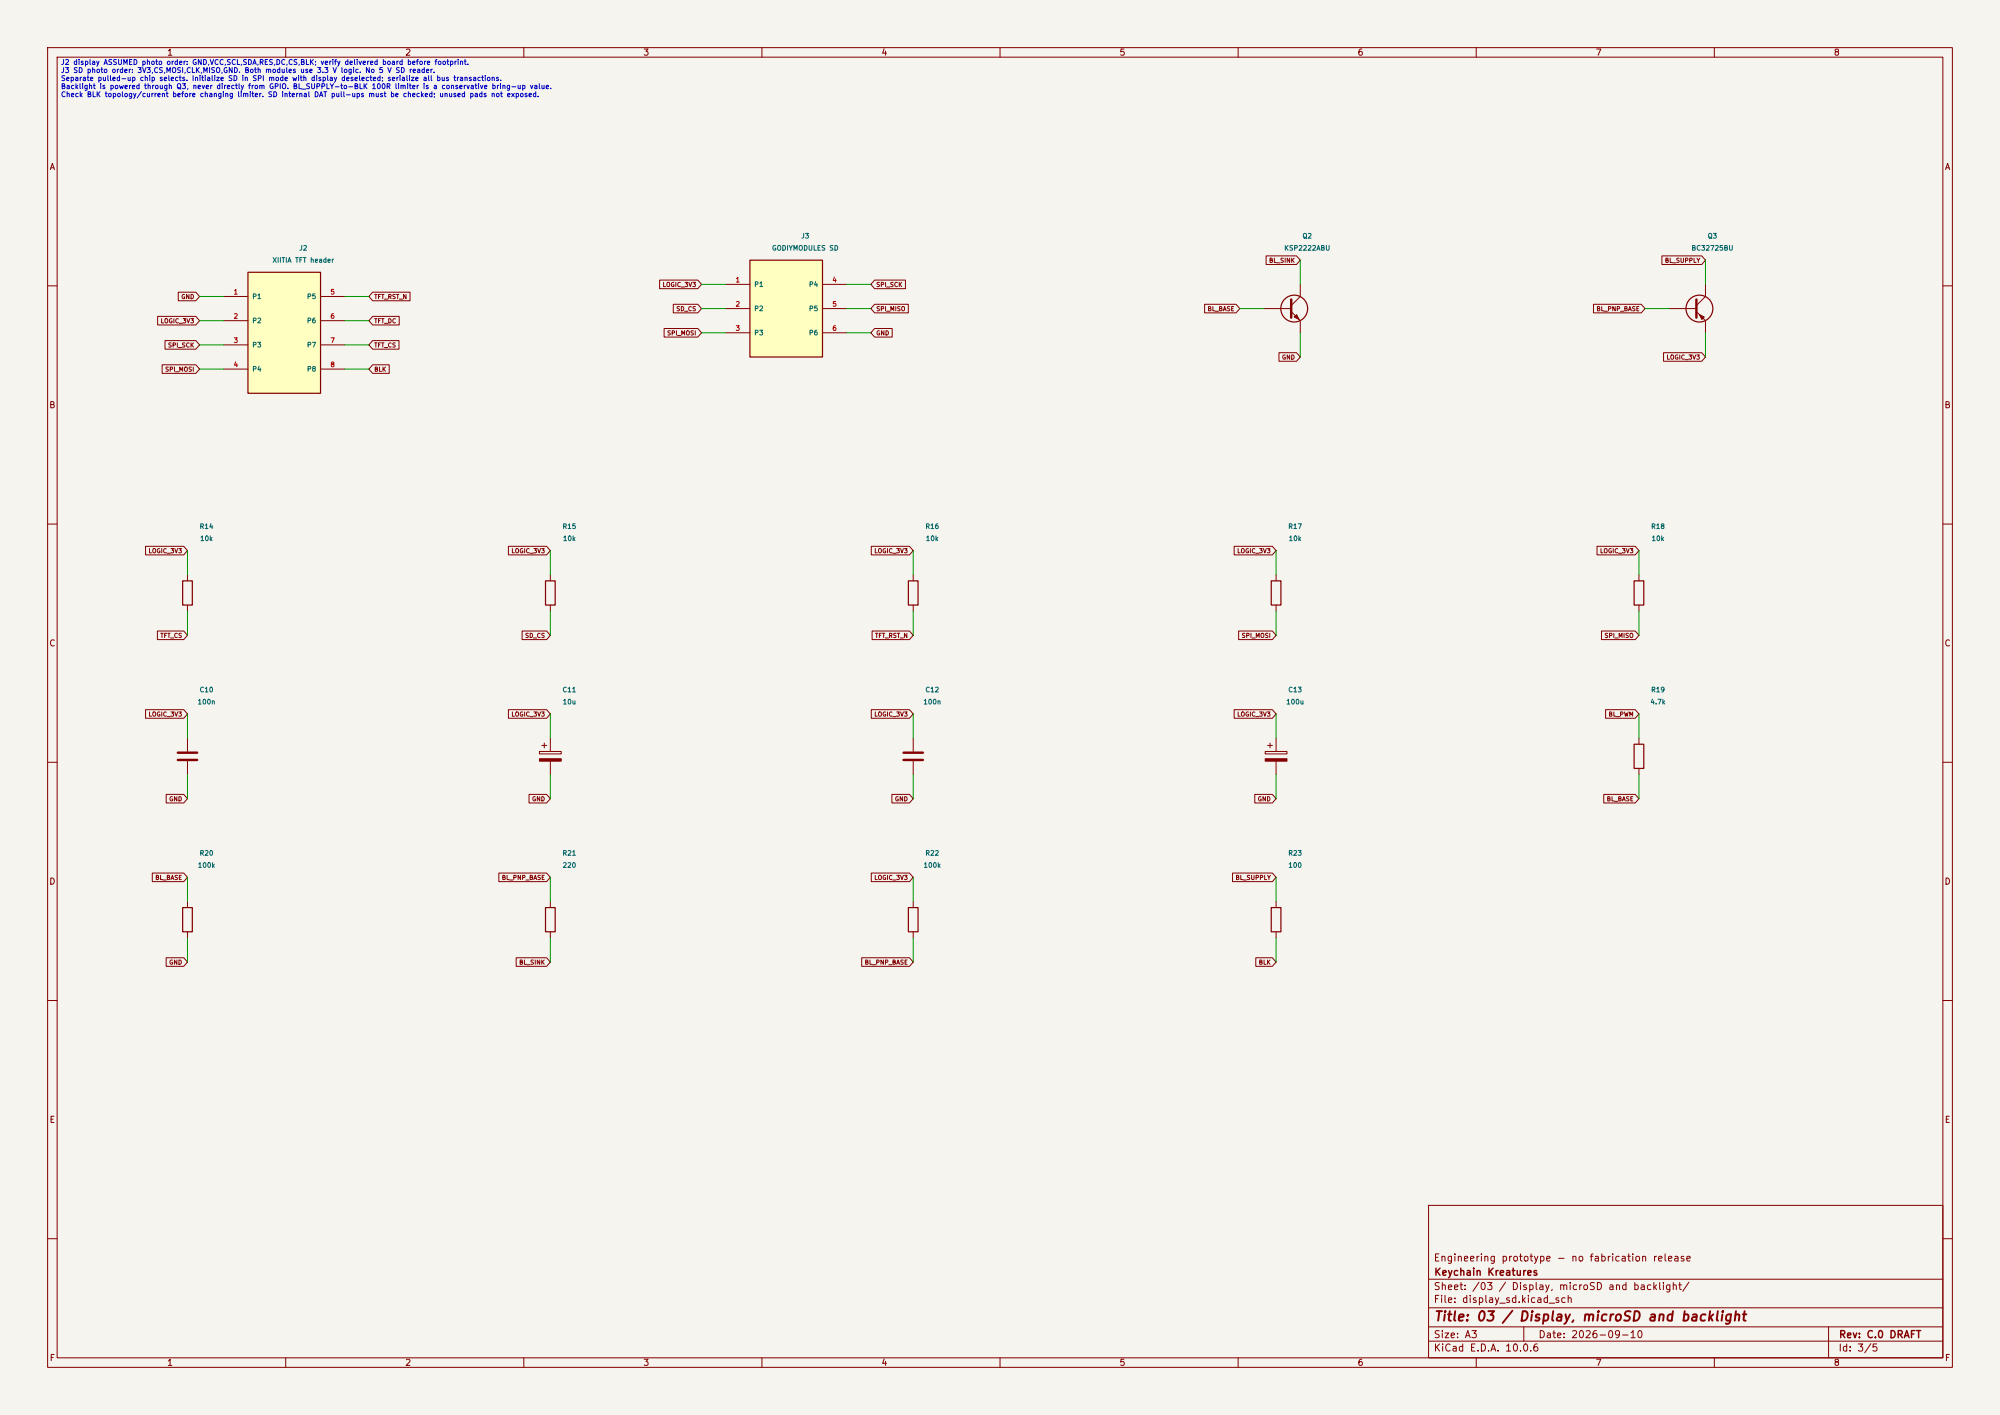
[picture p51: page 3]

J2 display ASSUMED photo order: GND,VCC,SCL,SDA,RES,DC,CS,BLK; verify delivered board before footprint. J3 SD photo order: 3V3,CS,MOSI,CLK,MISO,GND. Both modules use 3.3 V logic. No 5 V SD reader. Separate pulled-up chip selects. Initialize SD in SPI mode with display deselected; serialize all bus transactions. Backlight is powered through Q3, never directly from GPIO. BL_SUPPLY-to-BLK 100R limiter is a conservative bring-up value. Check BLK topology/current before changing limiter. SD internal DAT pull-ups must be checked; unused pads not exposed.

Engineering prototype - no fabrication release
Keychain Kreatures
Sheet: /03 / Display, microSD and backlight/
File: display_sd.kicad_sch
Title: 03 / Display, microSD and backlight

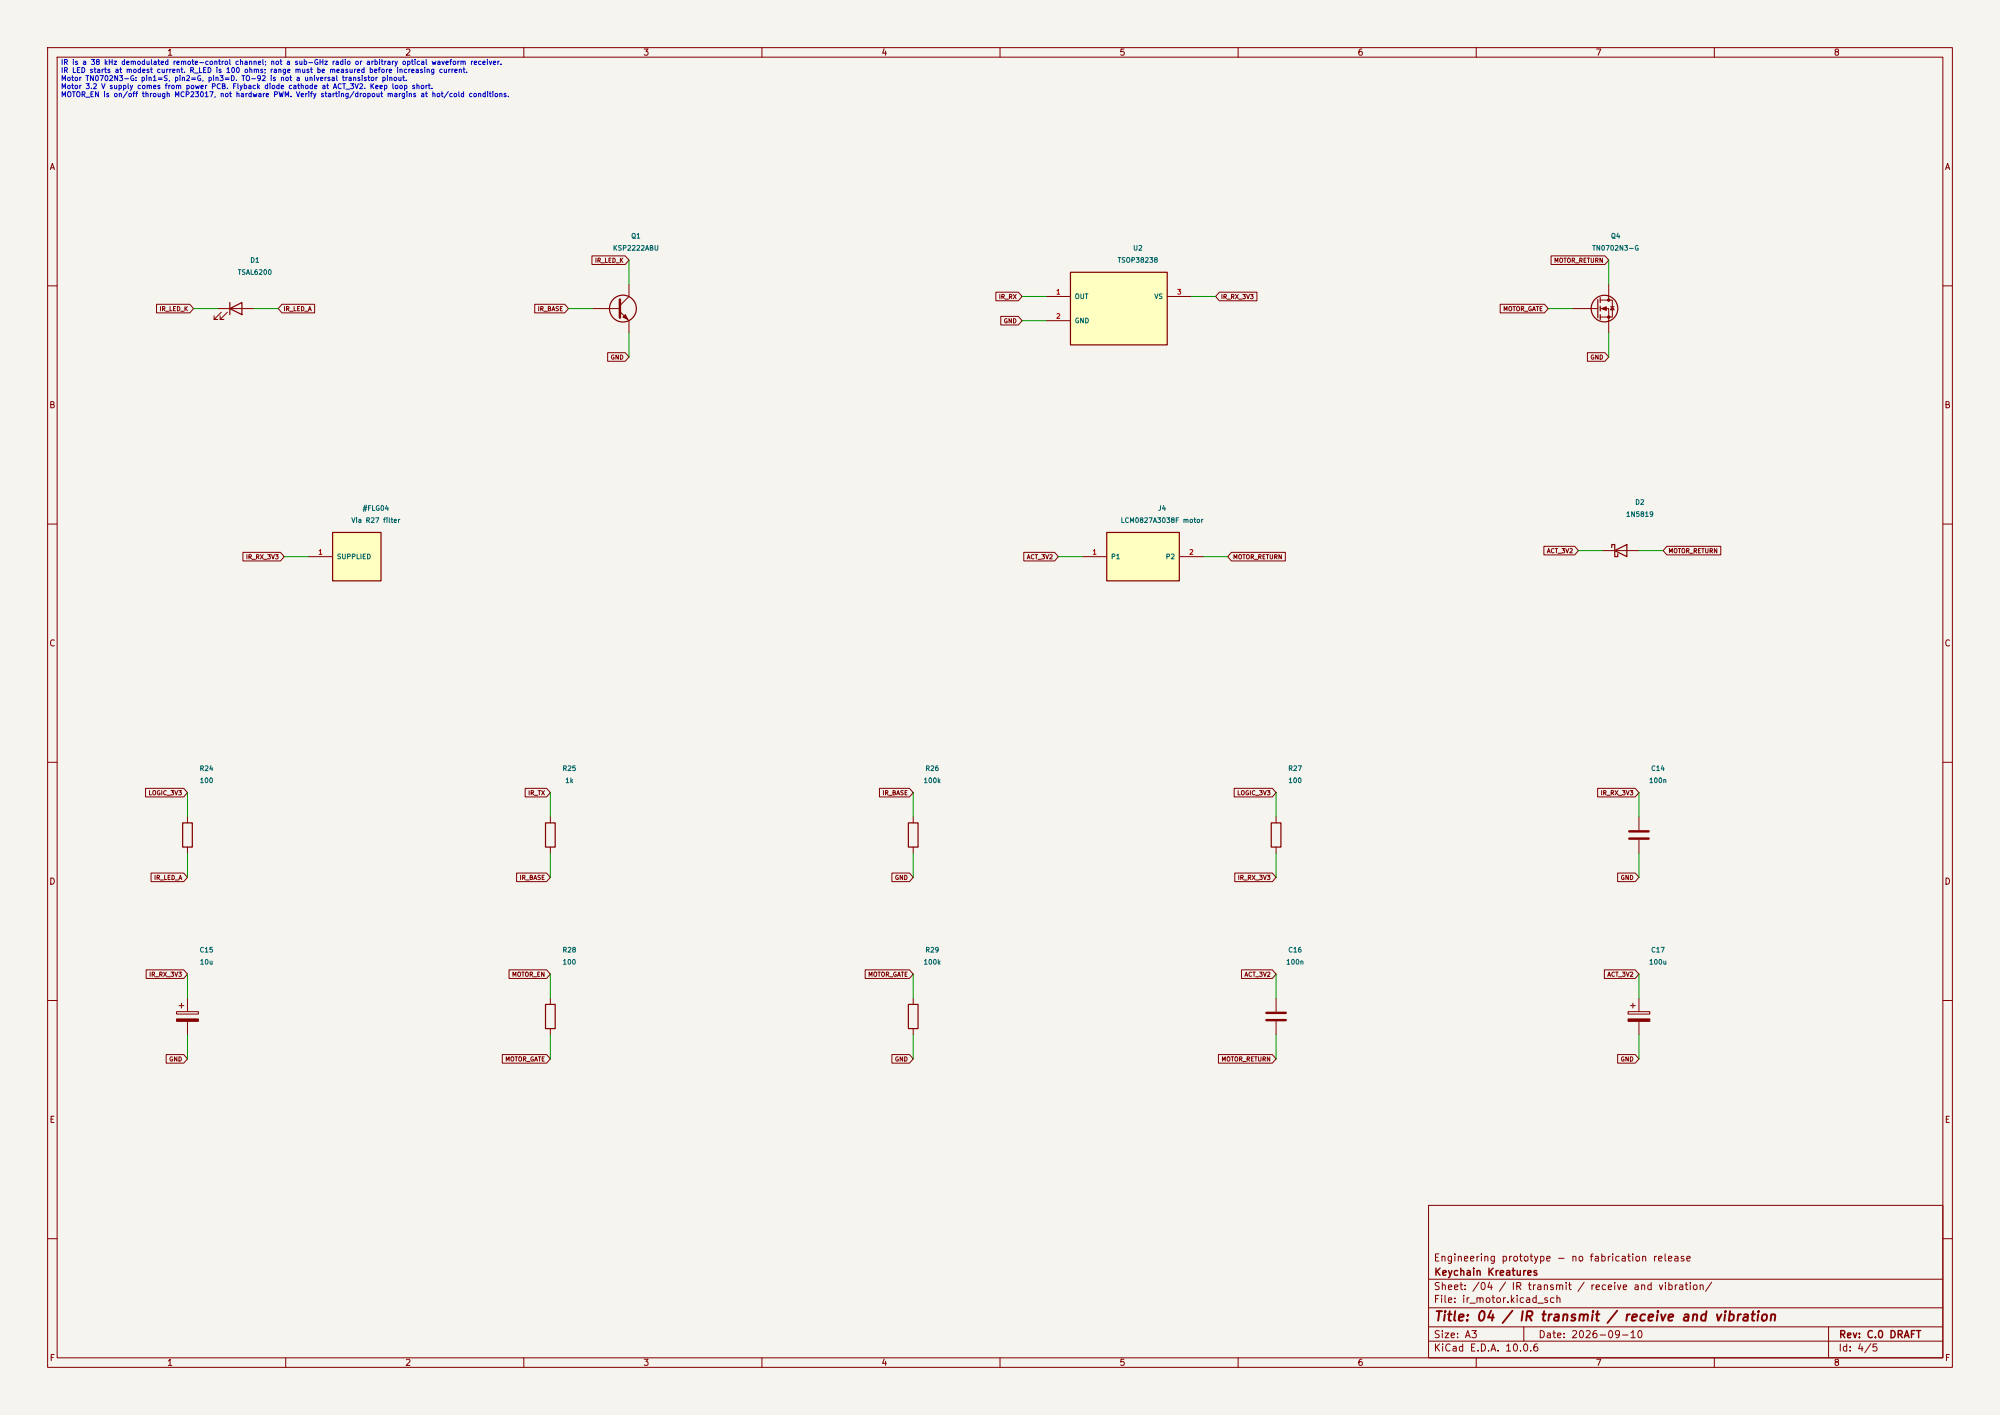
[picture p52: page 4]

IR is a 38 kHz demodulated remote-control channel; not a sub-GHz radio or arbitrary optical waveform receiver.
IR LED starts at modest current. R_LED is 100 ohms; range must be measured before increasing current. Motor TN0702N3-G: pin1=S, pin2=G, pin3=D. TO-92 is not a universal transistor pinout. Motor 3.2 V supply comes from power PCB. Flyback diode cathode at ACT_3V2. Keep loop short. MOTOR_EN is on/off through MCP23017, not hardware PWM. Verify starting/dropout margins at hot/cold conditions.

Engineering prototype - no fabrication release
Keychain Kreatures
Sheet: /04 / IR transmit / receive and vibration/
File: ir_motor.kicad_sch
Title: 04 / IR transmit / receive and vibration

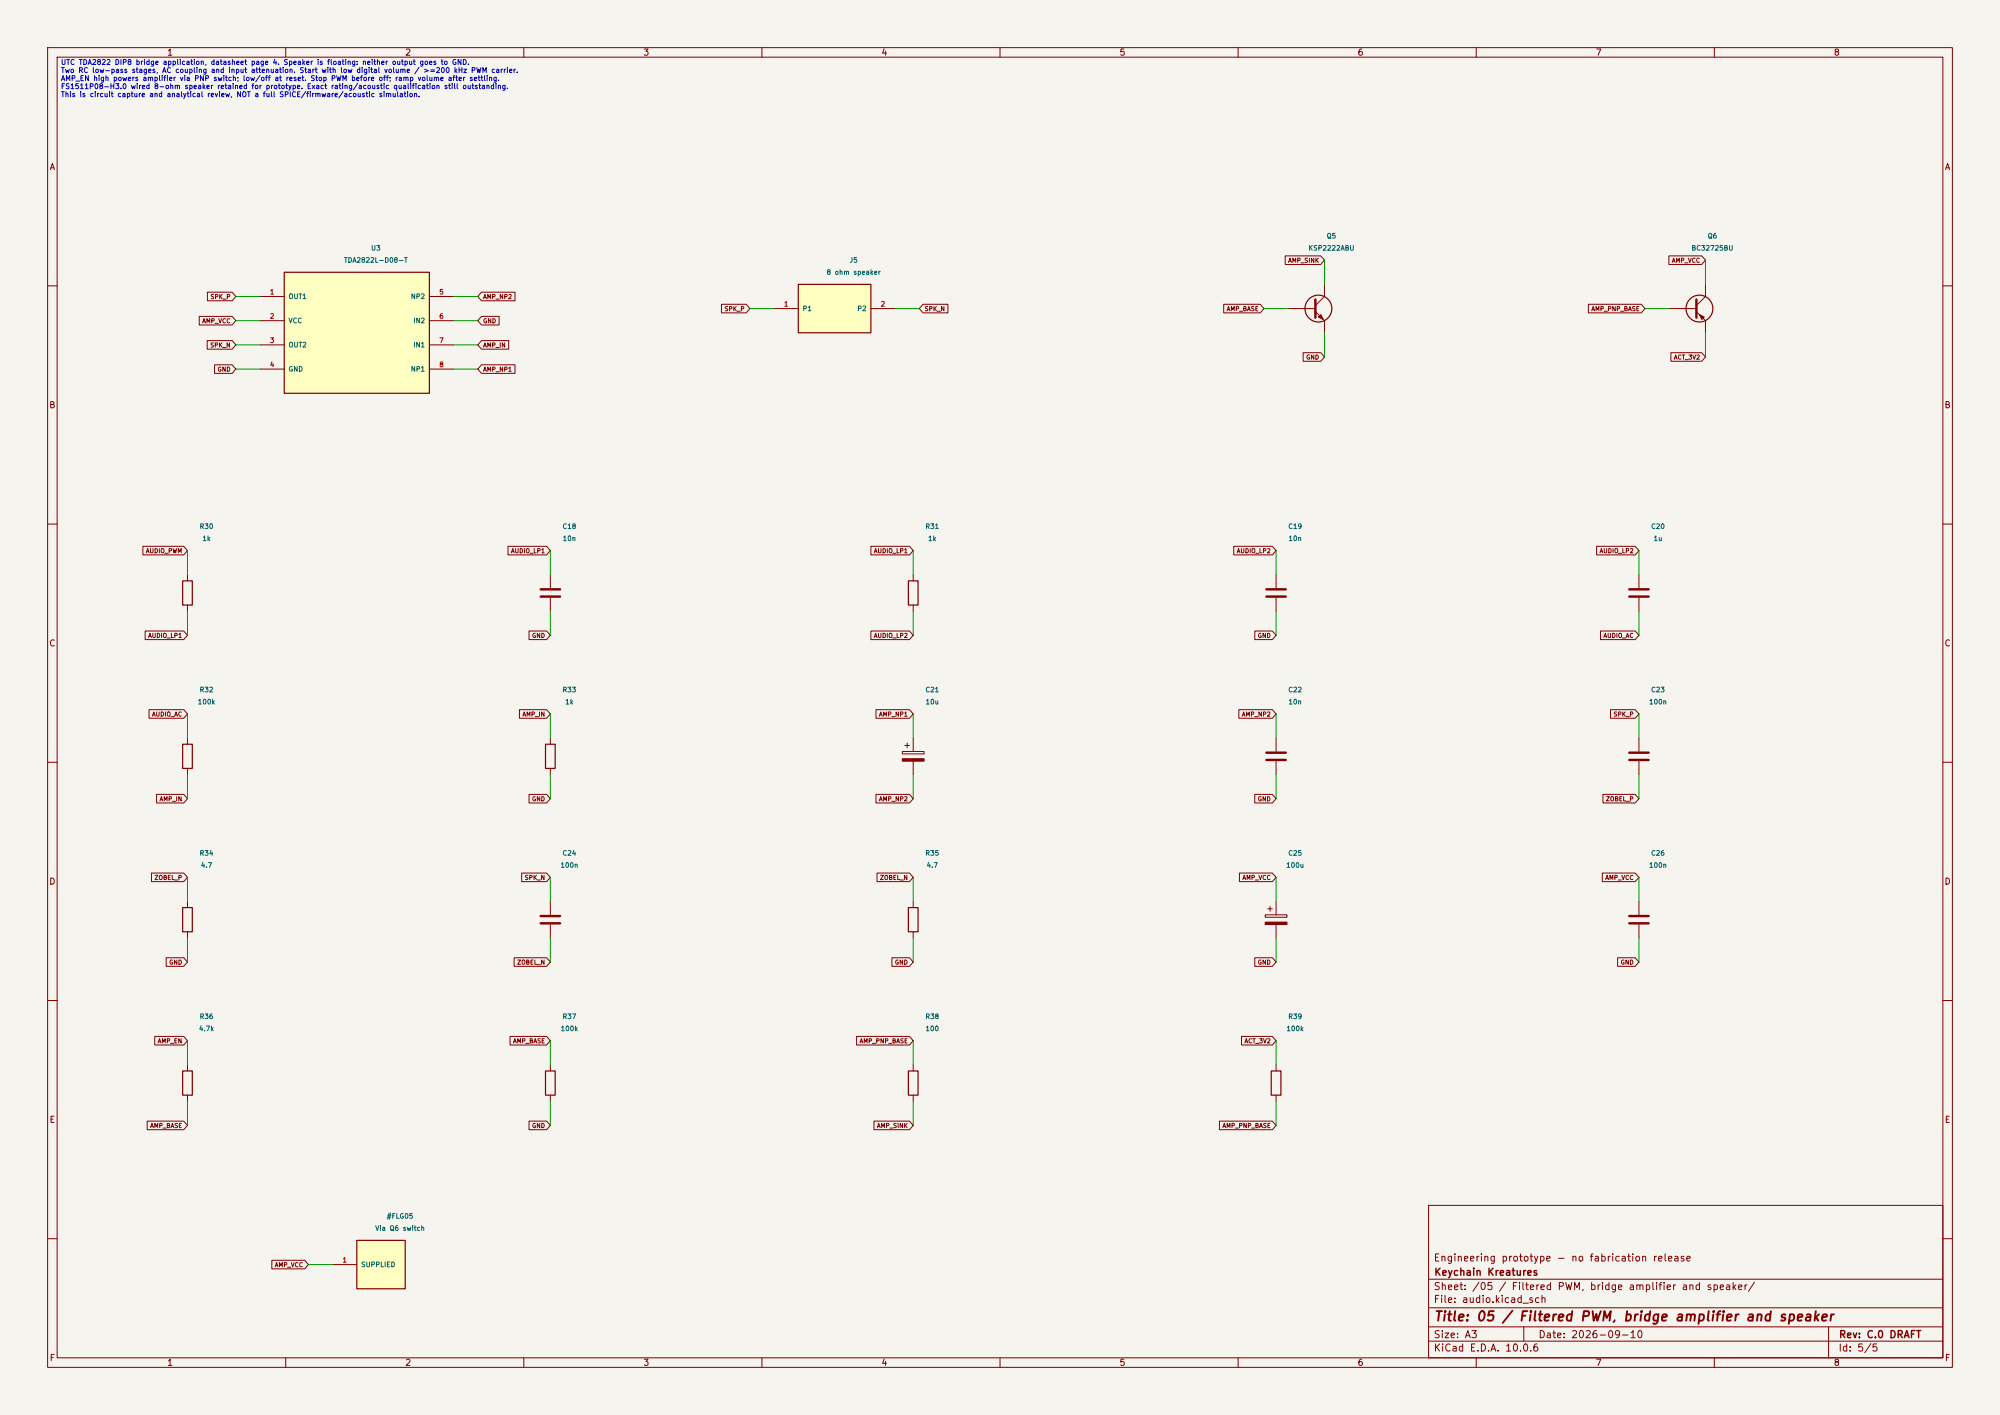
[picture p53: page 5]

AMP_IN UTC TDA2822 DIP8 bridge application, datasheet page 4. Speaker is floating: neither output goes to GND. Two RC low-pass stages, AC coupling and input attenuation. Start with low digital volume / >=200 kHz PWM carrier. AMP_EN high powers amplifier via PNP switch; low/off at reset. Stop PWM before off; ramp volume after settling. FS1511P08-H3.0 wired 8-ohm speaker retained for prototype. Exact rating/acoustic qualification still outstanding. This is circuit capture and analytical review, NOT a full SPICE/firmware/acoustic simulation.

Engineering prototype - no fabrication release
Keychain Kreatures
Sheet: /05 / Filtered PWM, bridge amplifier and speaker/
File: audio.kicad_sch
Title: 05 / Filtered PWM, bridge amplifier and speaker
