lionsarmor/KeychainKreatures/revisions/2026-09-12_current_only/KK_main_module/component_review/replacement_sources/nano.pdf

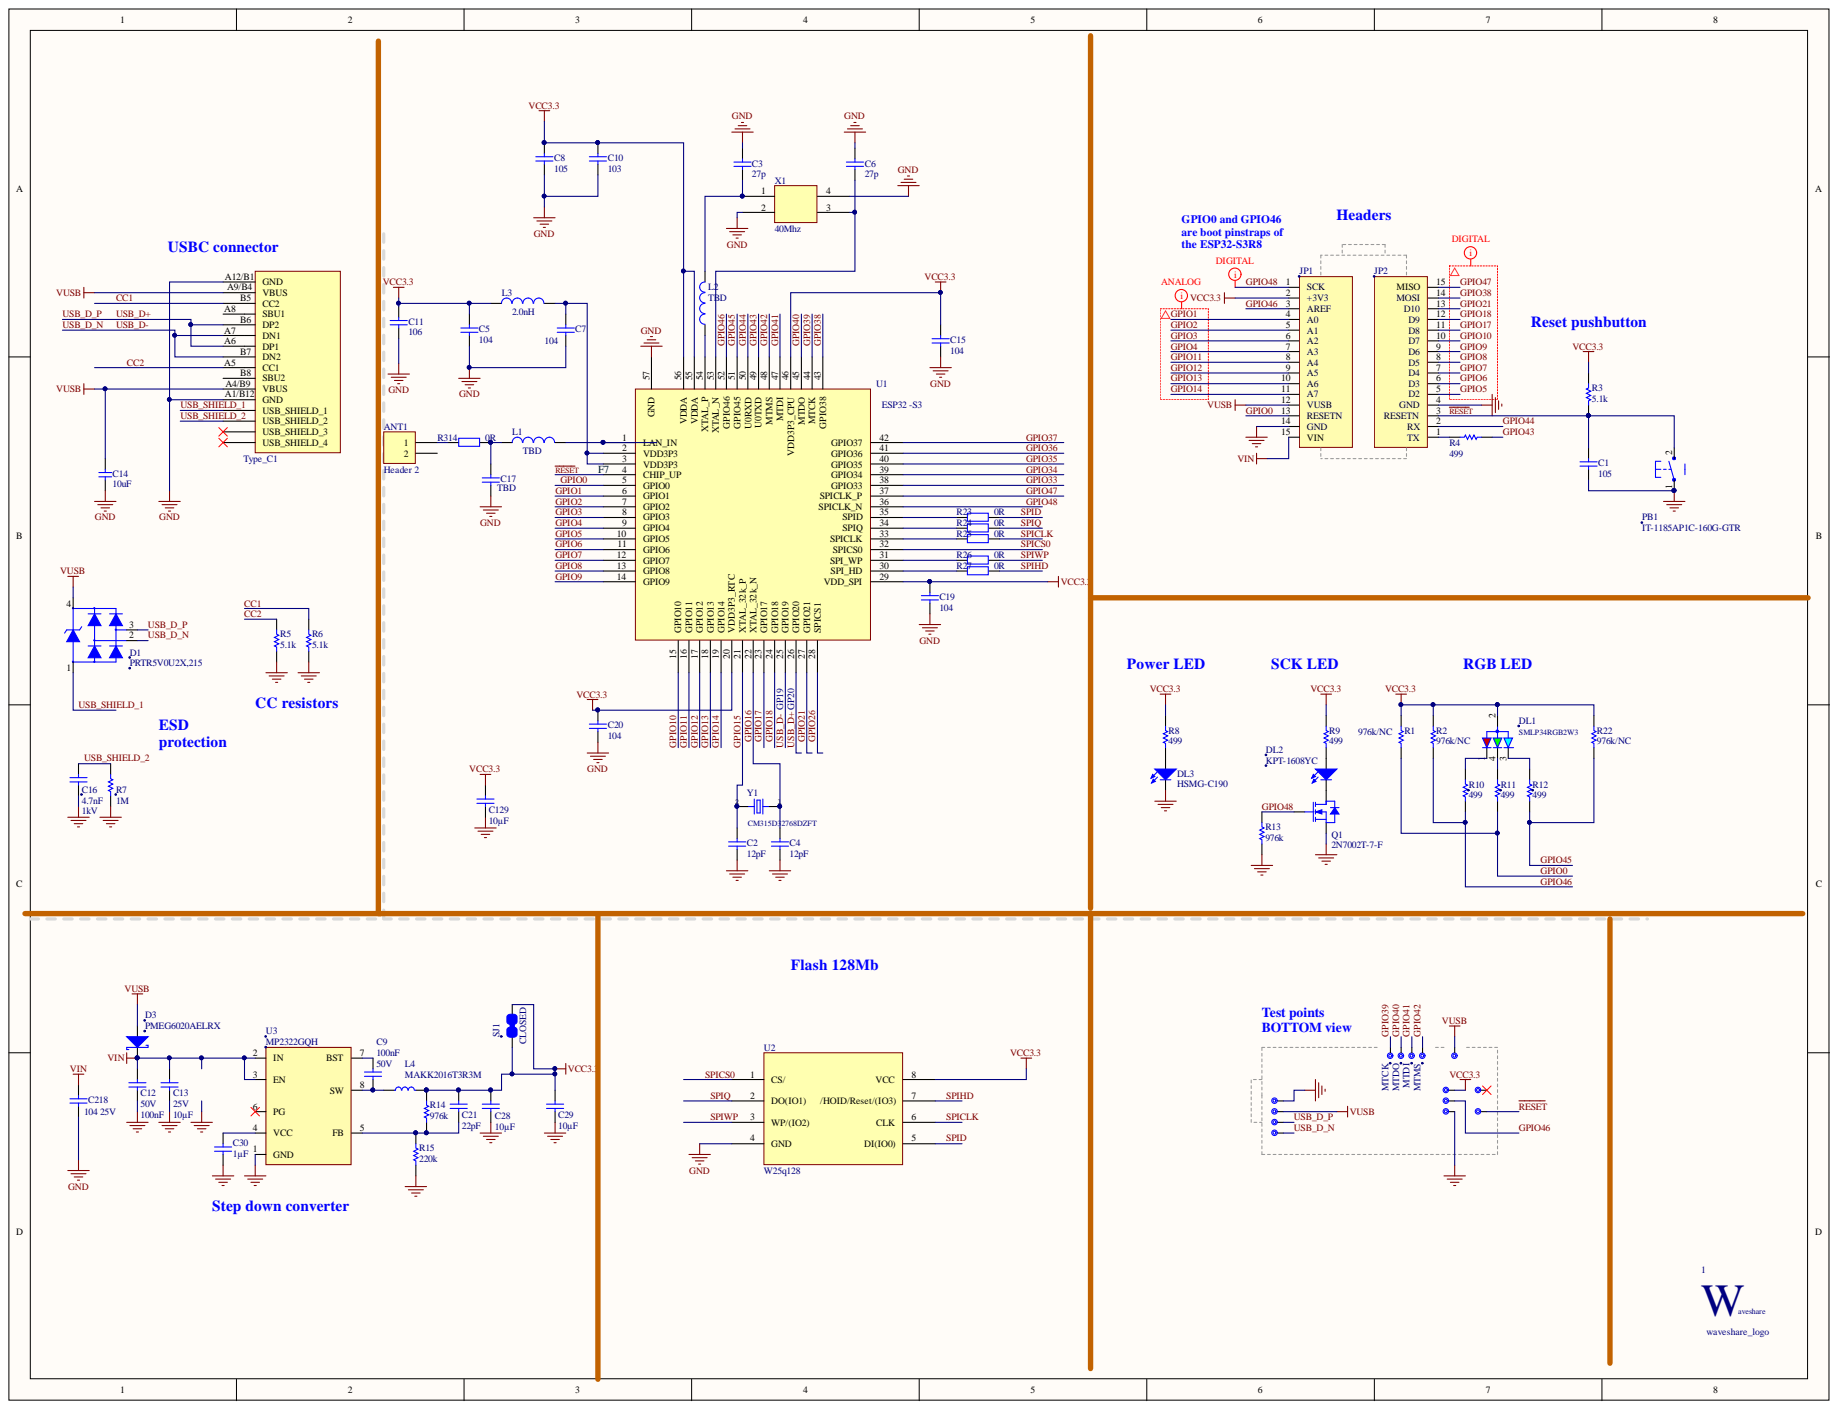
[picture p54: page 1]

GPIO0 and GPIO46
are boot pinstraps of
the ESP32-S3R8

GPIO38 43 MTCK 44 MTDO 45 VDD3P3_CPU 46 MTDI 47 MTMS 48 U0TXD 49 U0RXD 50

VDD3P3 2 | GPIO36
VDD3P3 3 | GPIO35
