lionsarmor/KeychainKreatures/revisions/2026-09-11_cleanup/KK_power_module/manufacturing/release/KK_power_module_0.2-LR1/schematic.pdf

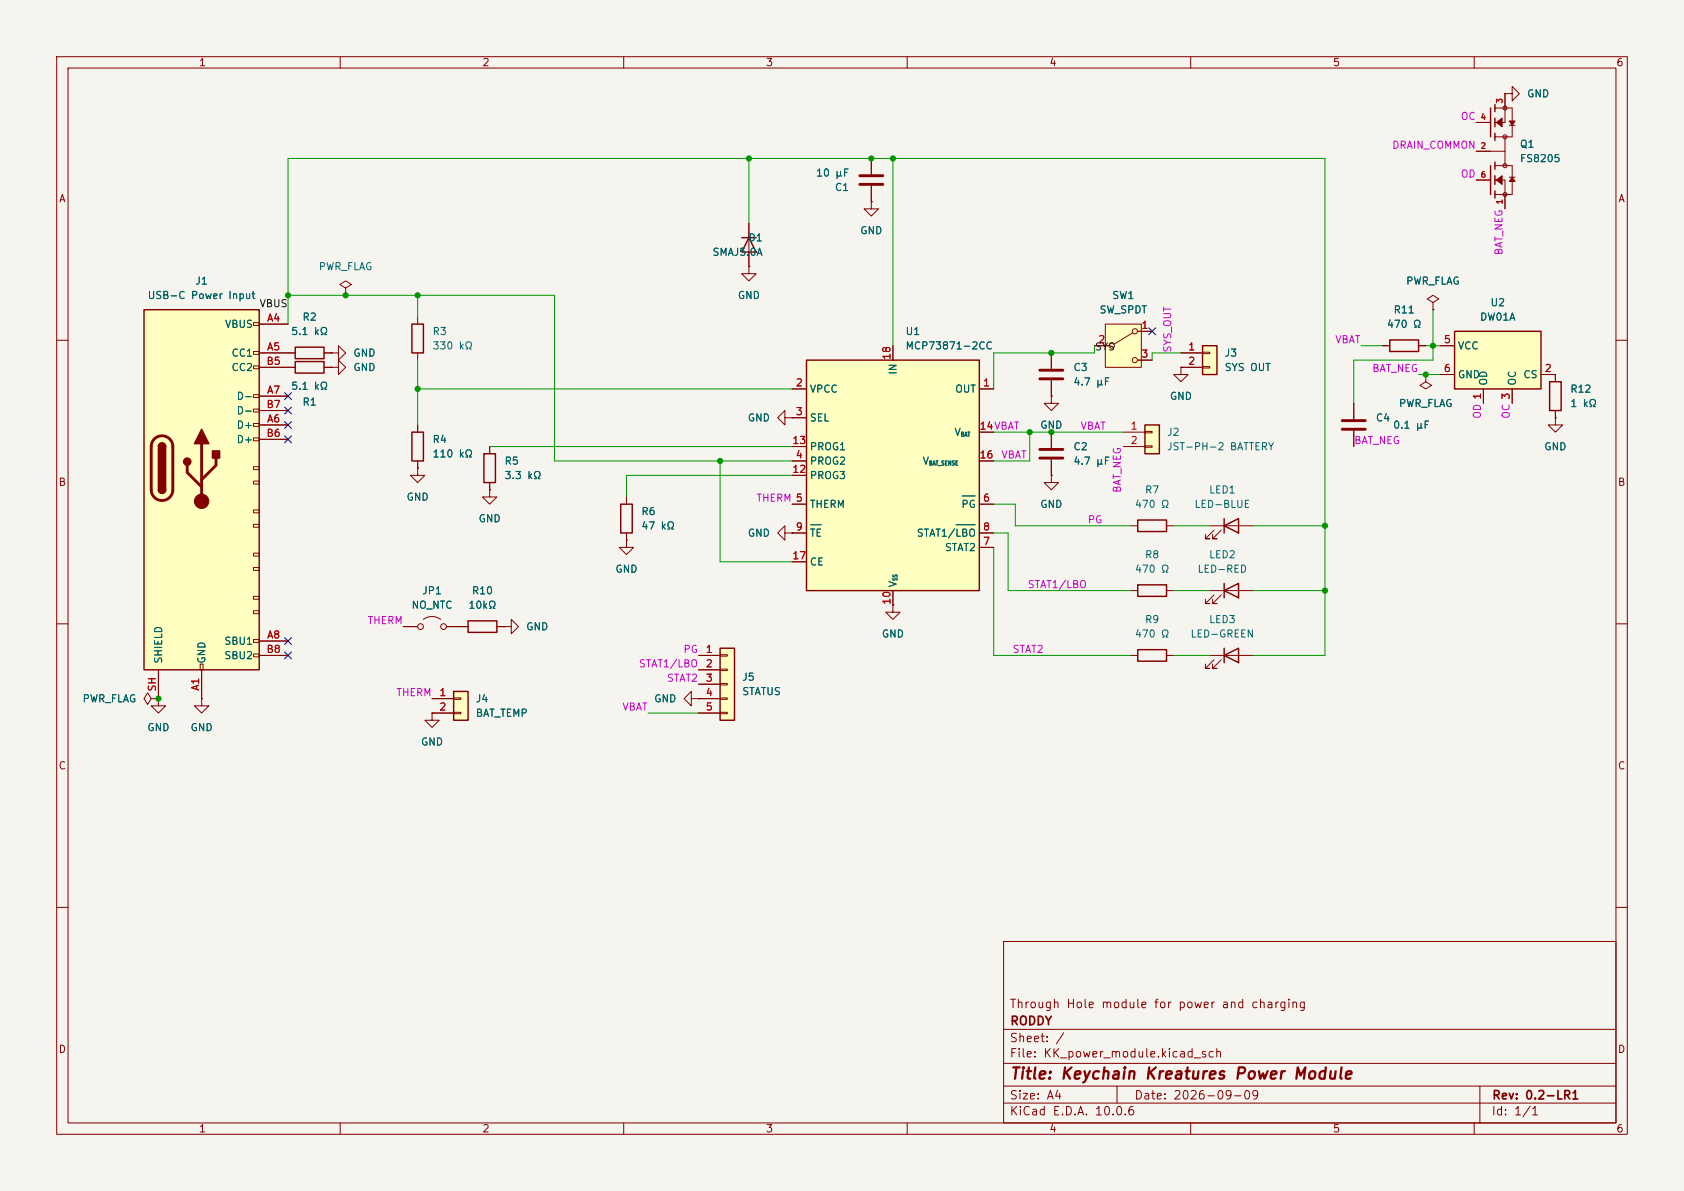
[picture p55: page 1]

J1 USB-C Power Input GND A1

Through Hole module for power and charging
RODDY
Sheet: /
File: KK_power_module.kicad_sch
Title: Keychain Kreatures Power Module

Size: A4 | Rev: 0.2-LR1
KiCad E.D.A. 10.0.6 | Id: 1/1
