lionsarmor/KeychainKreatures/PCBWay/01_Main_C6/02_Drawings_and_Reference/KK_main_module-assembly_bottom.pdf

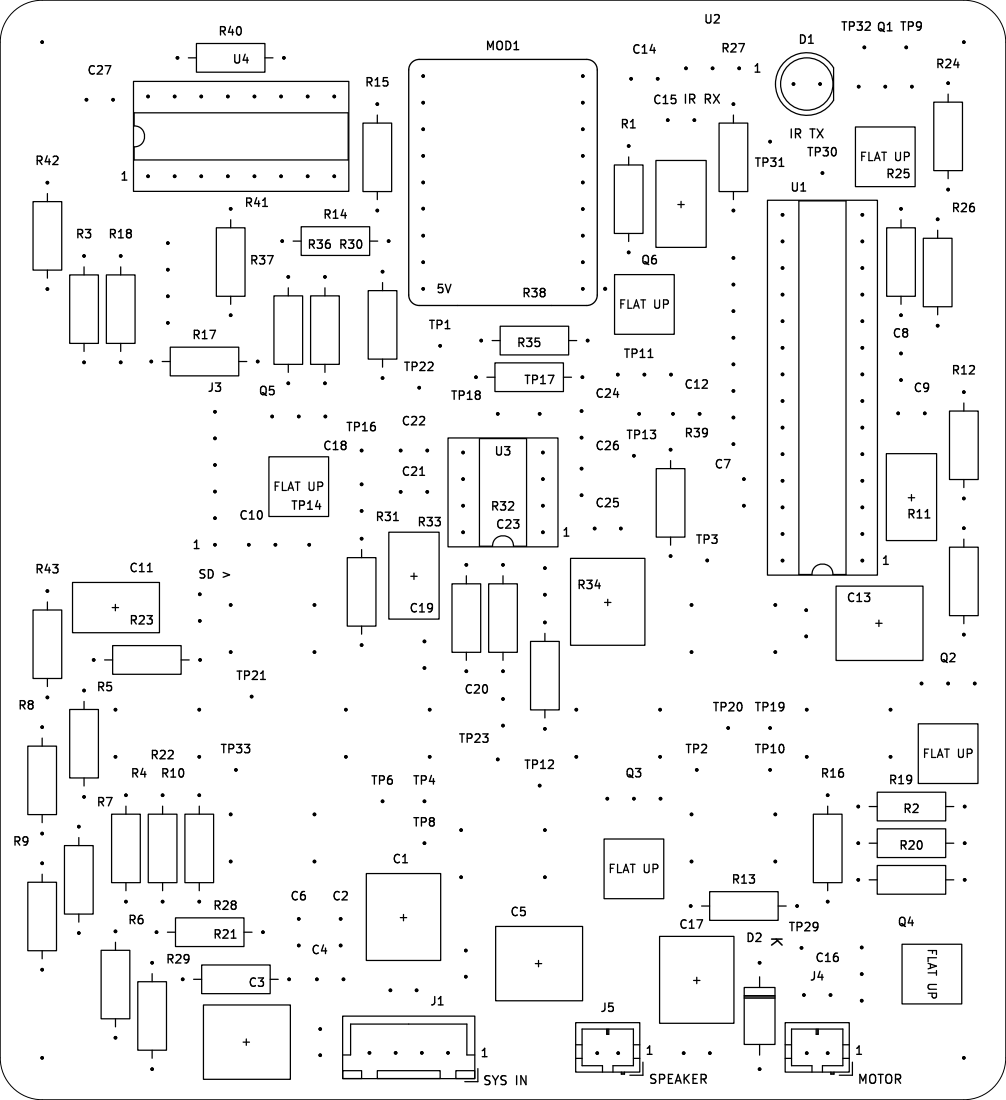
[picture p56: page 1]
