lionsarmor/KeychainKreatures/PCBWay/01_Main_C6/02_Drawings_and_Reference/KK_main_module-assembly_top.pdf

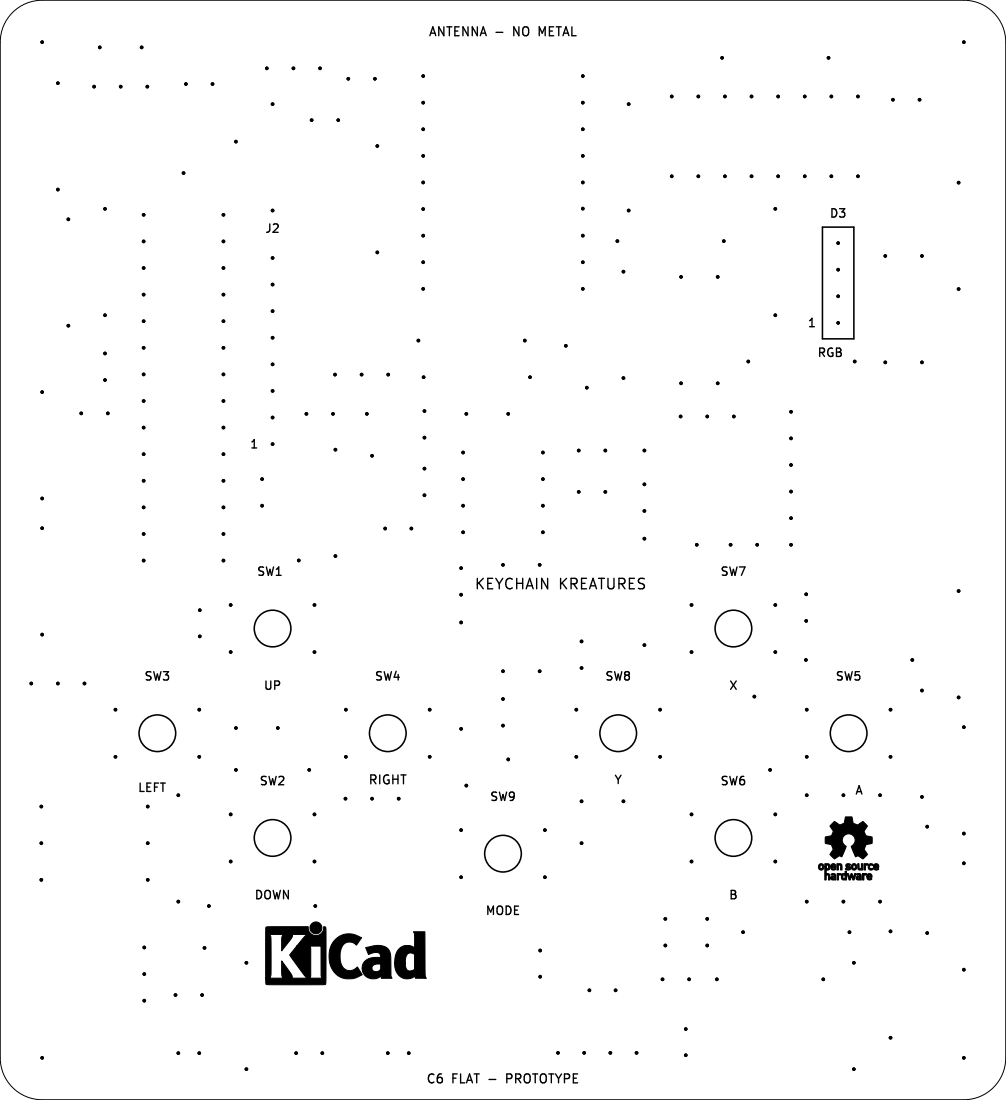
[picture p57: page 1]
