lionsarmor/KeychainKreatures/PCBWay/02_Power_P4/04_Assembly_Drawings/KK_power_module-assembly_bottom.pdf

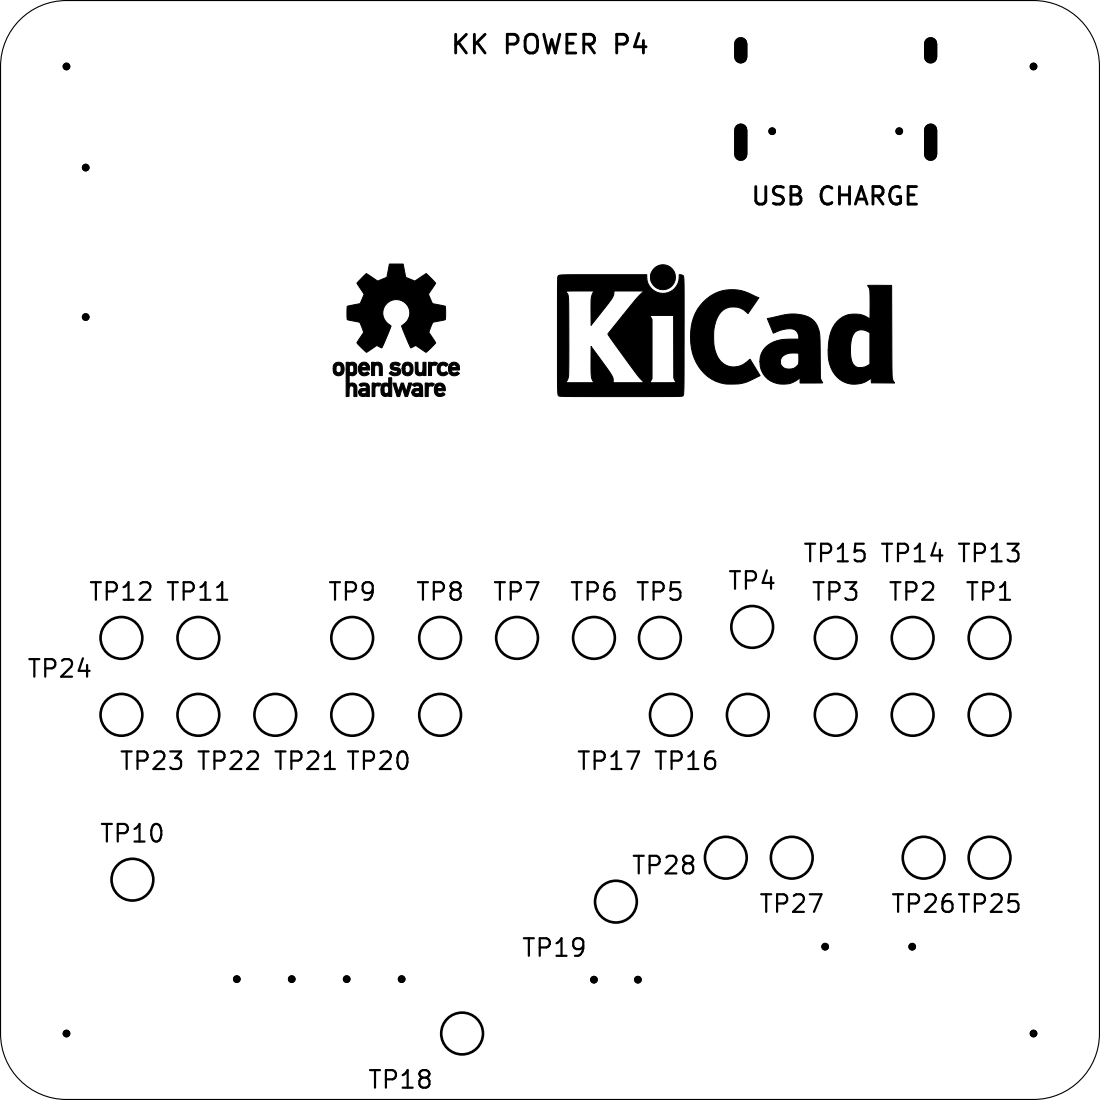
[picture p58: page 1]
