lionsarmor/KeychainKreatures/PCBWay/02_Power_P4/04_Assembly_Drawings/KK_power_module-assembly_top.pdf

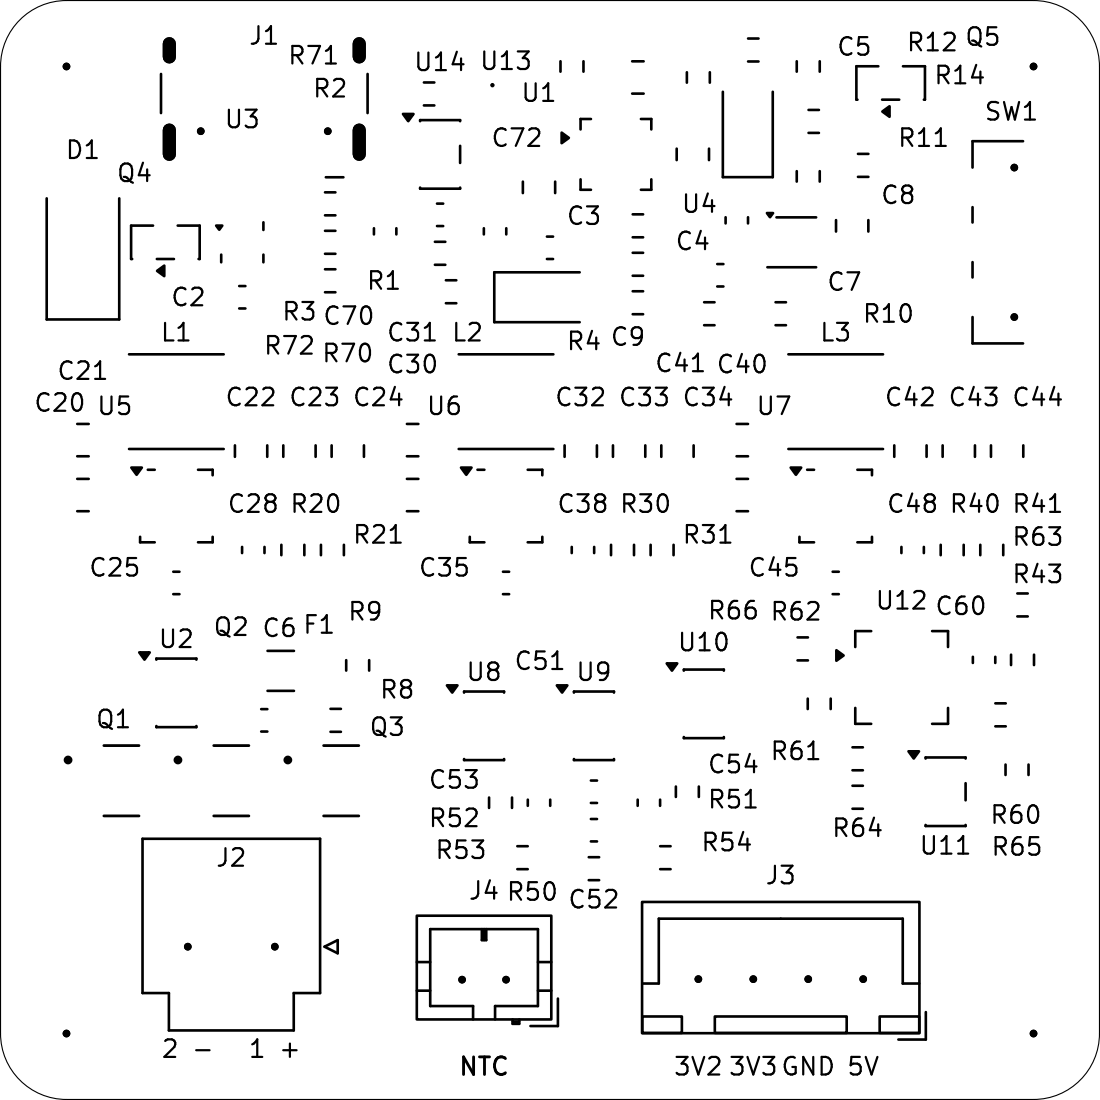
[picture p59: page 1]
