lionsarmor/KeychainKreatures/PCBWay/02_Power_P4/04_Assembly_Drawings/KK_power_module-bodies_bottom.pdf

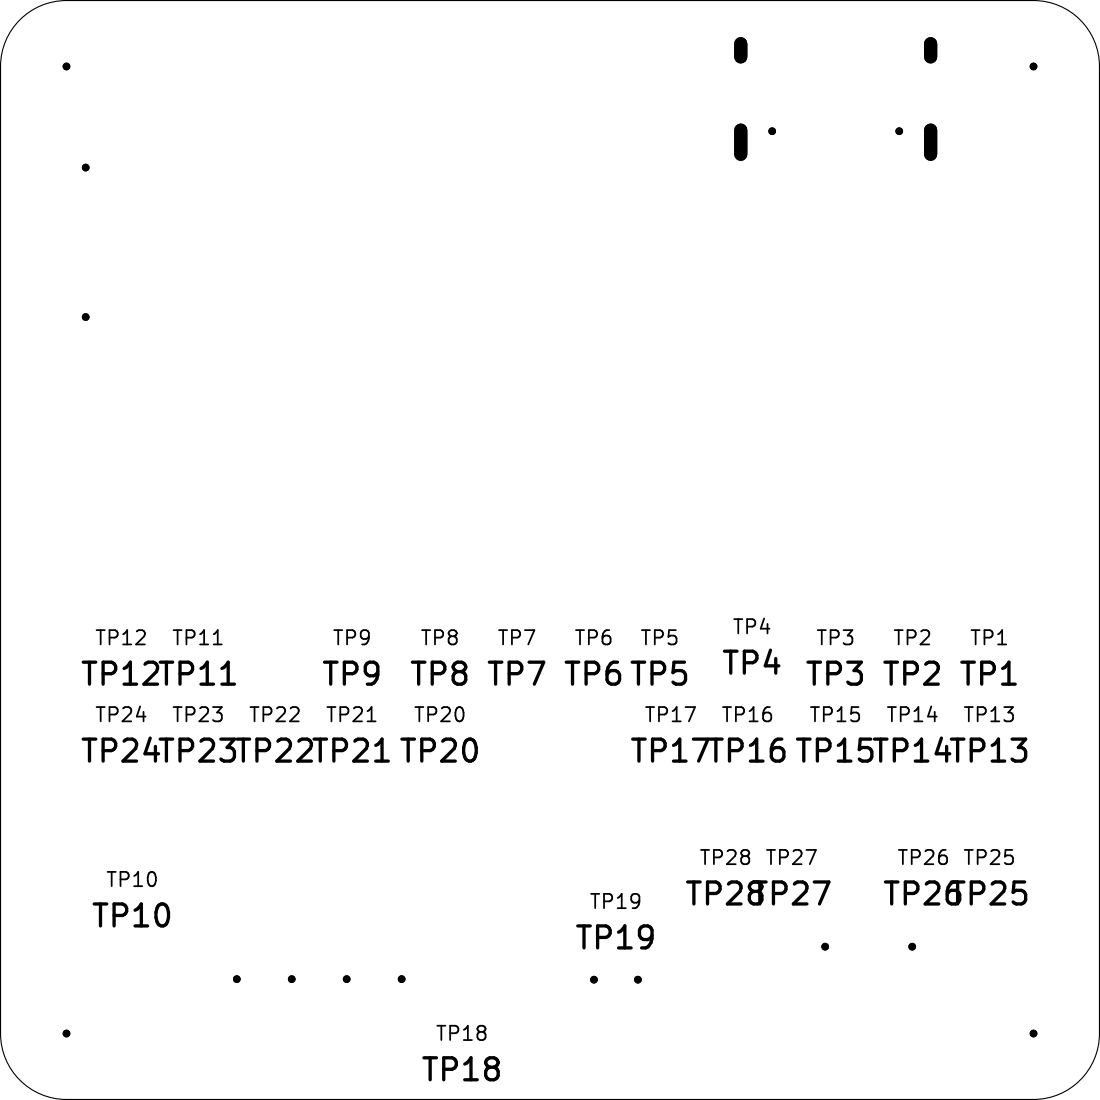
[picture p60: page 1]
