lionsarmor/KeychainKreatures/PCBWay/02_Power_P4/04_Assembly_Drawings/KK_power_module-bodies_top.pdf

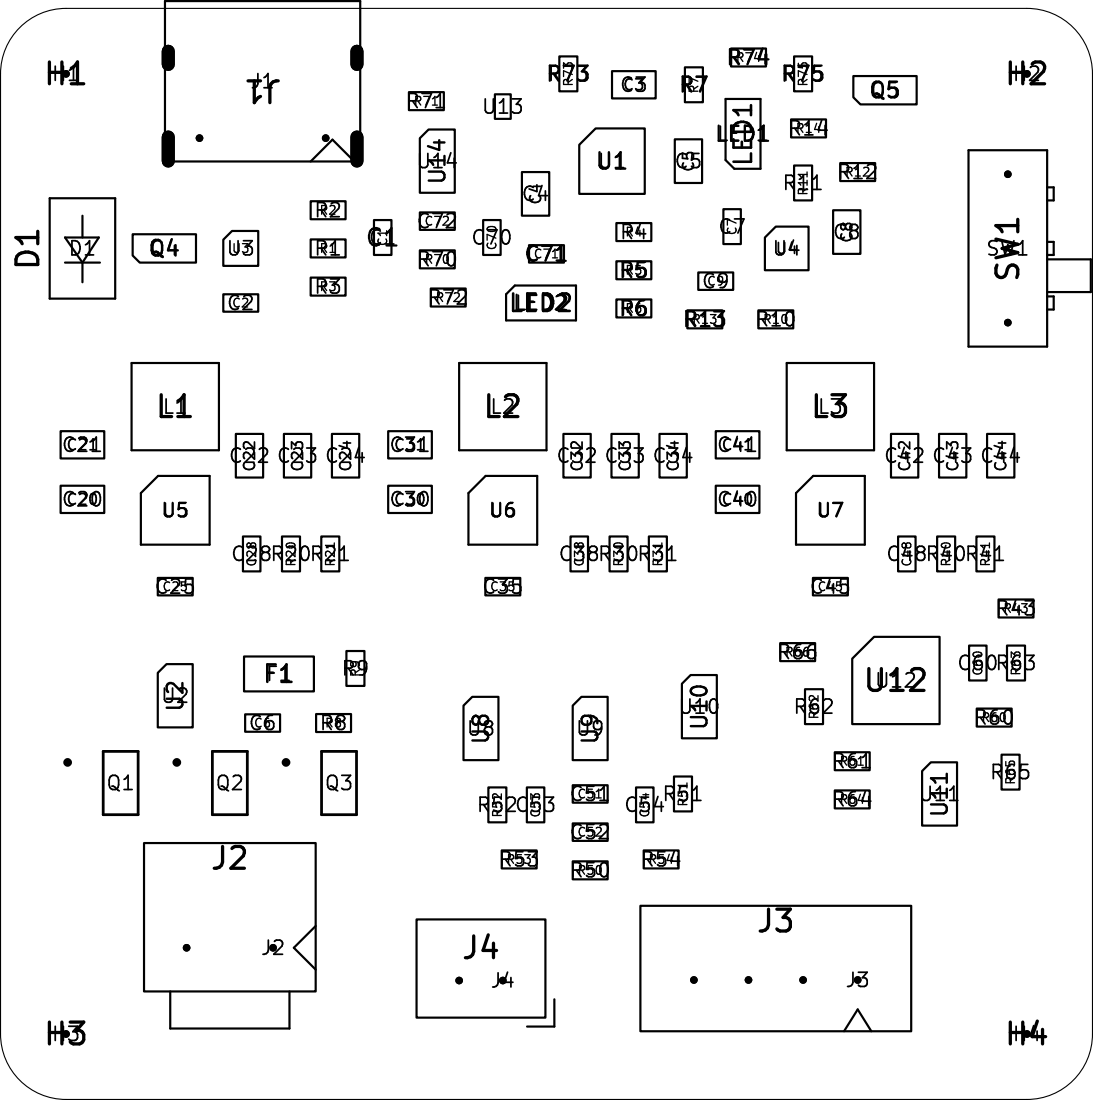
[picture p61: page 1]
