lionsarmor/KeychainKreatures/revisions/2026-09-11_cleanup/KK_power_module/manufacturing/release/KK_power_module_0.2-LR1/assembly_bottom.pdf

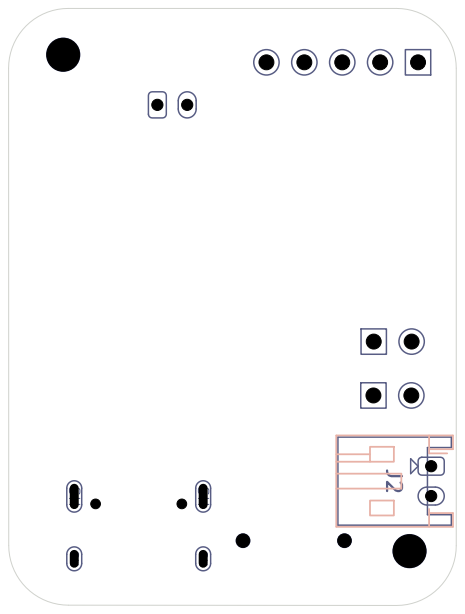
[picture p62: page 1]
