lionsarmor/KeychainKreatures/revisions/2026-09-12_power_compact/unissued_export_1/KK_main_module/manufacturing/KK_MAIN_C6_P4_PAIRING_5_PROTOTYPE_REVIEW_2026-09-12/drawings/KK_main_module-bodies_bottom.pdf

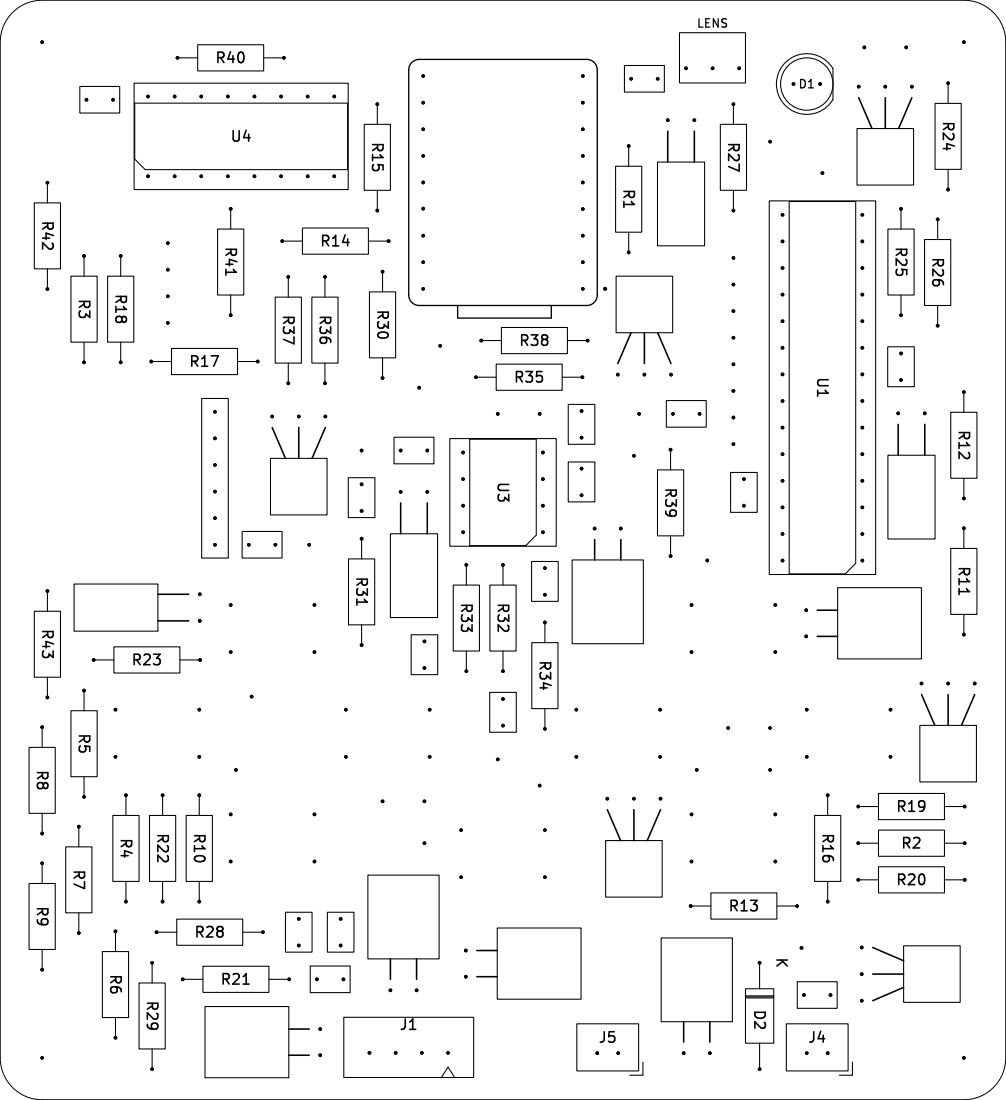
[picture p64: page 1]
