lionsarmor/KeychainKreatures/revisions/2026-09-12_current_only/KK_power_module/work/P2_logo_review/prototype_package/drawings/KK_power_module-assembly_bottom.pdf

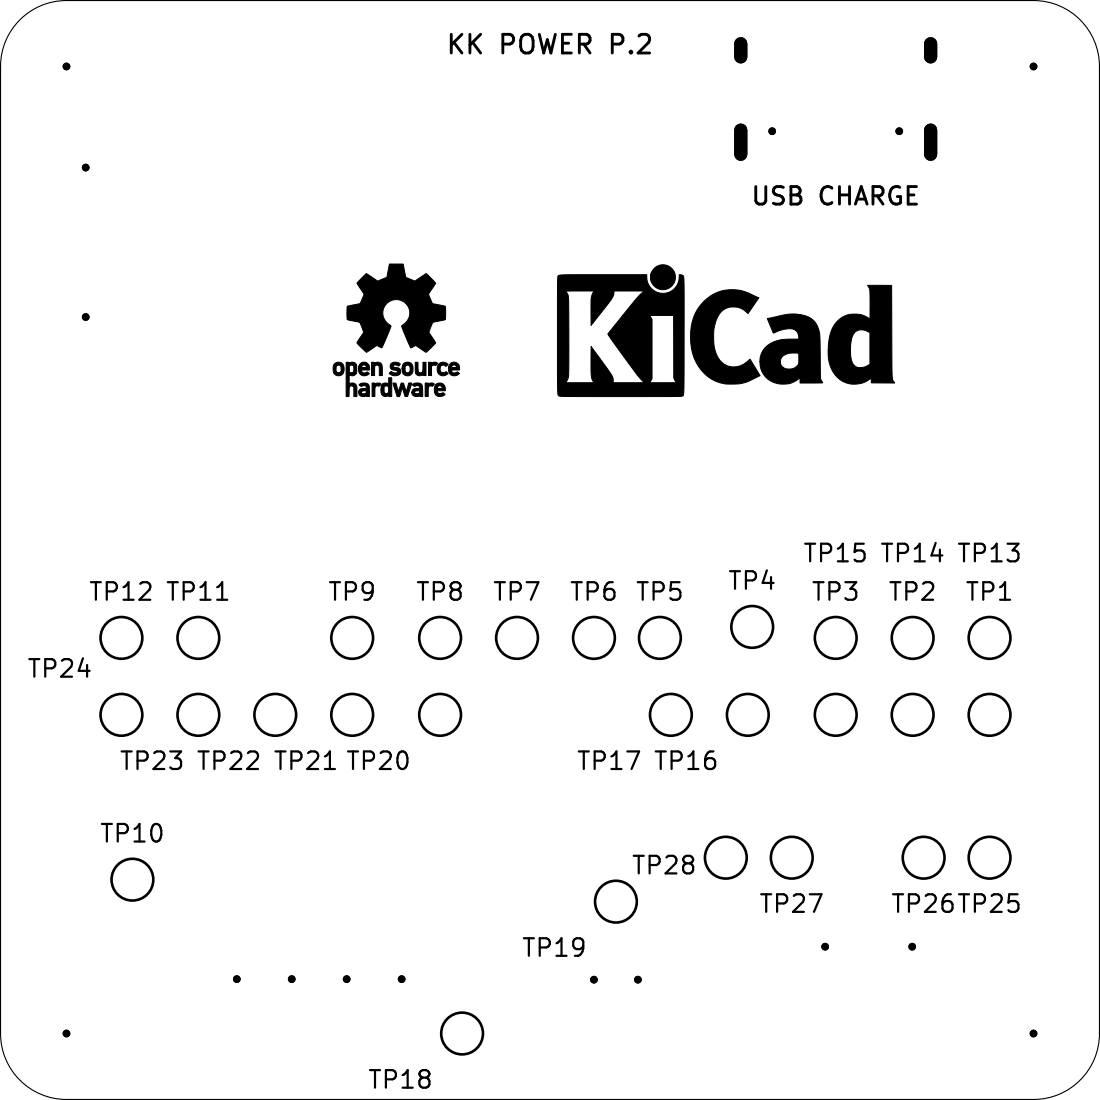
[picture p66: page 1]
