lionsarmor/KeychainKreatures/revisions/2026-09-11_cleanup/KK_main_module/pcb/backups/pre_c5_relayout/front-fit-check.pdf

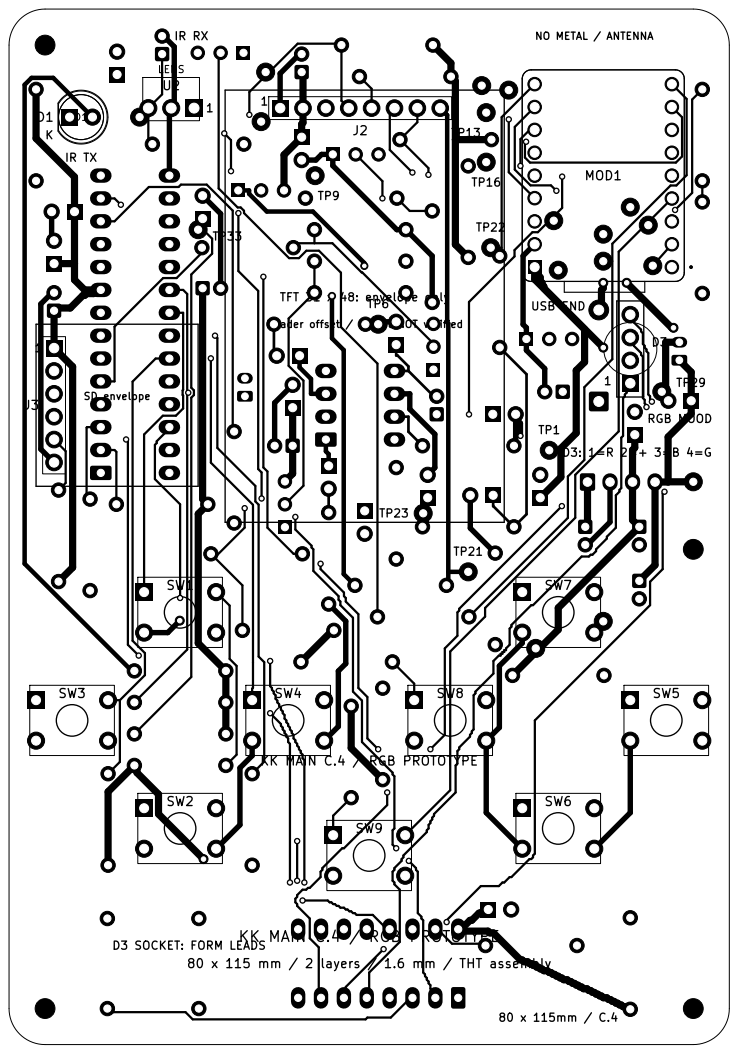
[picture p67: page 1]

IR TX D3 SOCKET: FORM LEADS
