lionsarmor/KeychainKreatures/revisions/2026-09-11_cleanup/KK_main_module/pcb/backups/pre_c5_relayout/back-fit-check.pdf

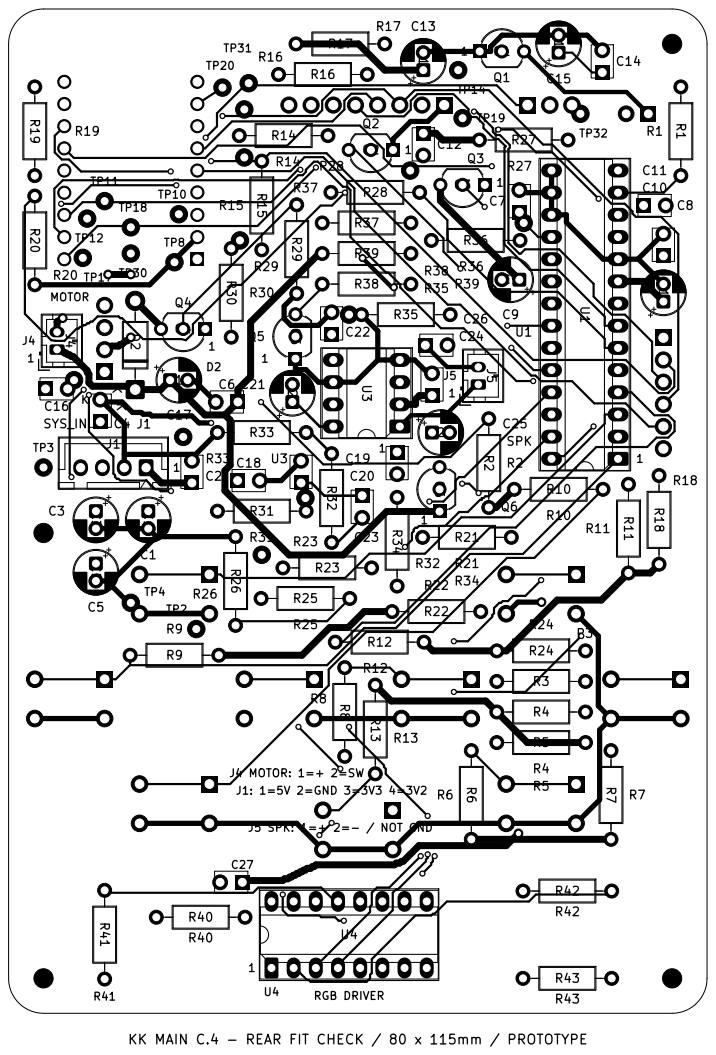
[picture p68: page 1]
