lionsarmor/KeychainKreatures/revisions/2026-09-12_power_compact/P3_previous/KK_power_module/manufacturing/KK_POWER_P3_5_PROTOTYPE_REVIEW_2026-09-12/drawings/KK_power_module-bodies_bottom.pdf

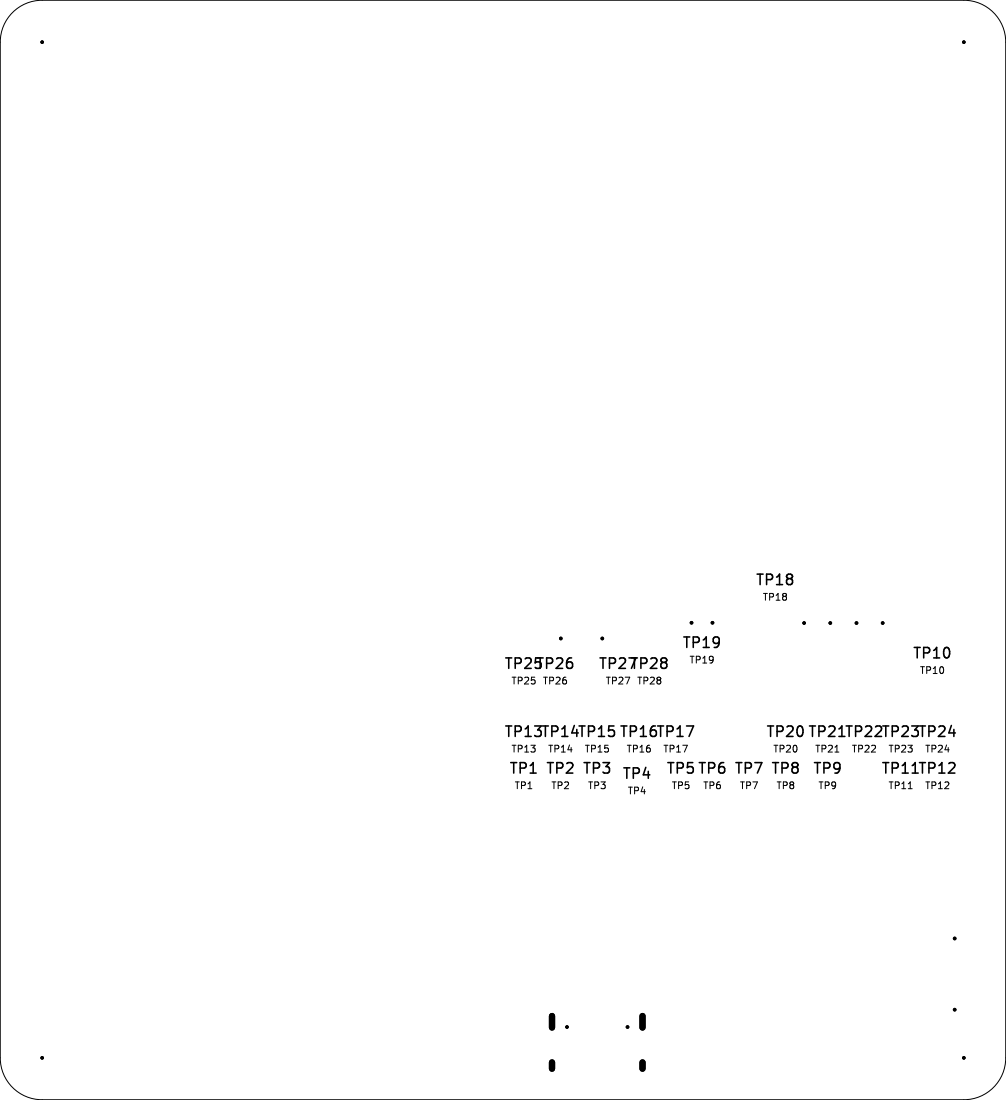
[picture p69: page 1]
