lionsarmor/KeychainKreatures/revisions/2026-09-11_cleanup/KK_power_module/KK_power_module.kicad_pcb

## KiCad design revisions/2026-09-11_cleanup/KK_power_module/KK_power_module.kicad_pcb (2026-09-12)

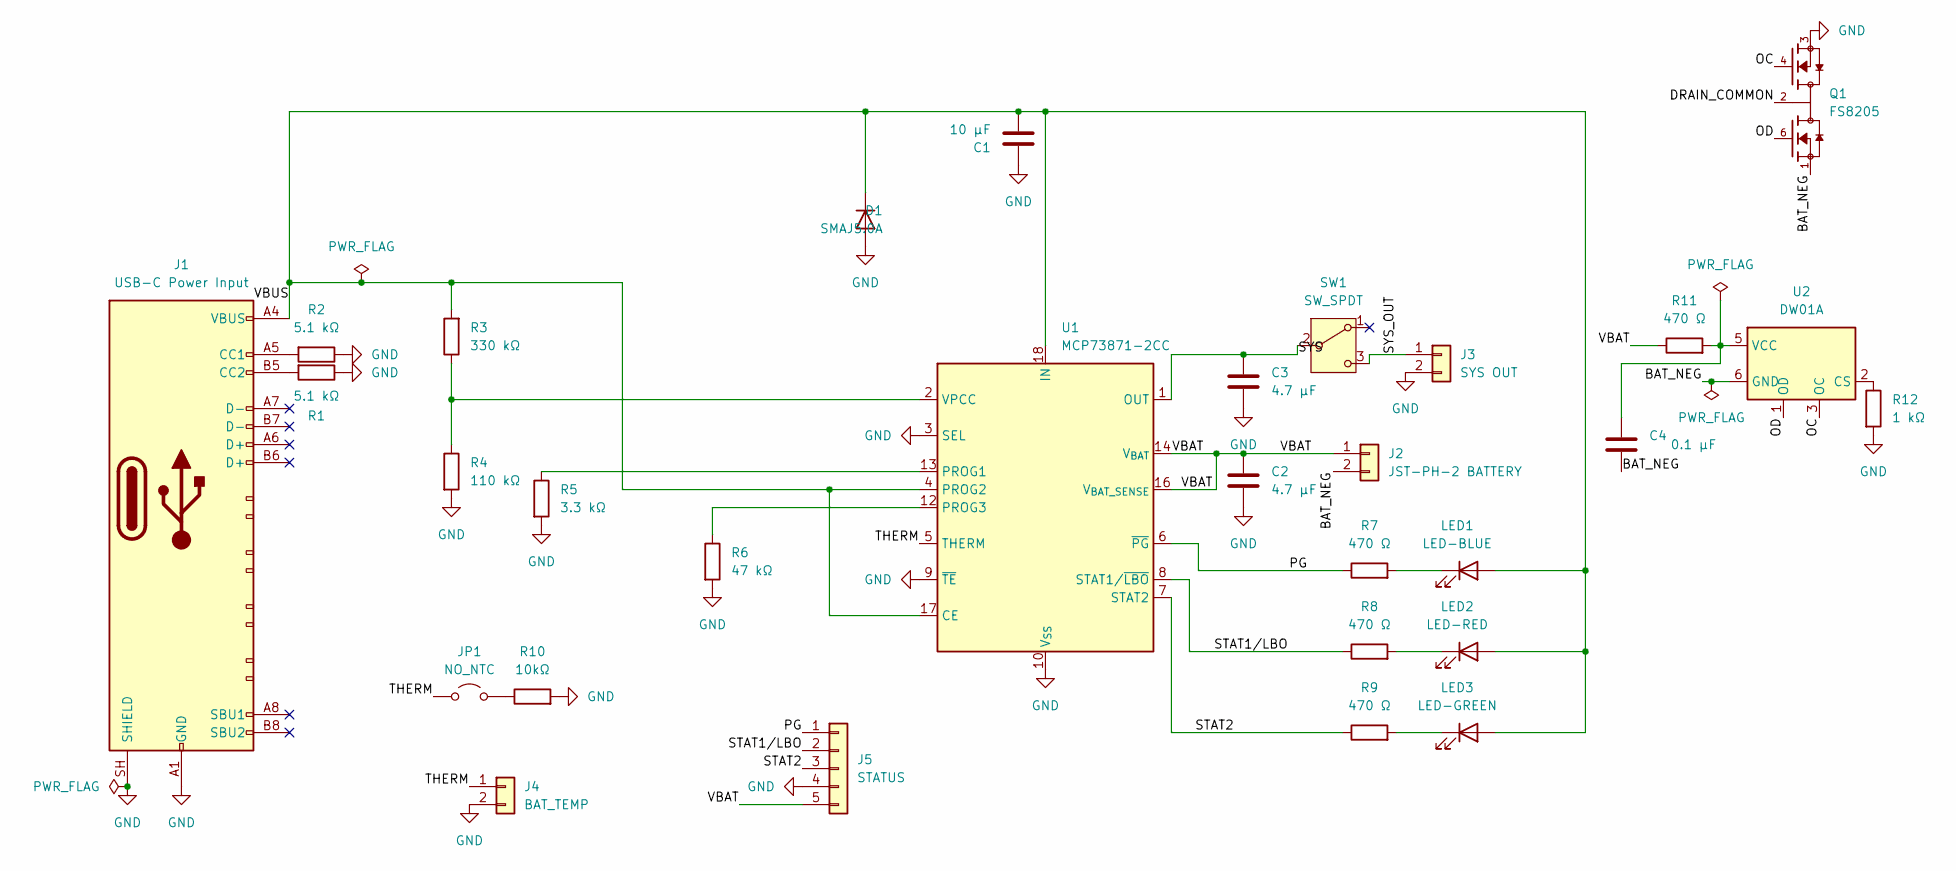
[picture p77: schematic KK_power_module.kicad_sch, Keychain Kreatures Power Module]

Parts:
C1: 10 µF; C_1206_3216Metric_Pad1.33x1.80mm_HandSolder
C2, C3: 4.7 µF; C_1206_3216Metric_Pad1.33x1.80mm_HandSolder
C4: 0.1 µF; C_1206_3216Metric_Pad1.33x1.80mm_HandSolder
D1: SMAJ5.0A; D_SMA_Handsoldering
J1: USB-C Power Input; USB_C_Receptacle_HCTL_HC-TYPE-C-16P-01A
J2: JST-PH-2 BATTERY; JST_PH_S2B-PH-K_1x02_P2.00mm_Horizontal
J3: SYS OUT; JST_PH_S2B-PH-K_1x02_P2.00mm_Horizontal
J4: BAT_TEMP; PinHeader_1x02_P2.54mm_Vertical
J5: STATUS; PinHeader_1x05_P2.54mm_Vertical
JP1: NO_NTC; PinHeader_1x02_P2.54mm_Vertical
LED1: LED-BLUE; LED_1206_3216Metric_Pad1.42x1.75mm_HandSolder
LED2: LED-RED; LED_1206_3216Metric_Pad1.42x1.75mm_HandSolder
LED3: LED-GREEN; LED_1206_3216Metric_Pad1.42x1.75mm_HandSolder
Q1: FS8205; SOT95P280X145-6N; PARTREV 1.9
R1, R2: 5.1 kΩ; R_1206_3216Metric_Pad1.30x1.75mm_HandSolder
R3: 330 kΩ; R_1206_3216Metric_Pad1.30x1.75mm_HandSolder
R4: 110 kΩ; R_1206_3216Metric_Pad1.30x1.75mm_HandSolder
R5: 3.3 kΩ; R_1206_3216Metric_Pad1.30x1.75mm_HandSolder
R6: 47 kΩ; R_1206_3216Metric_Pad1.30x1.75mm_HandSolder
R7, R8, R9, R11: 470 Ω; R_1206_3216Metric_Pad1.30x1.75mm_HandSolder
R10: 10kΩ; R_1206_3216Metric_Pad1.30x1.75mm_HandSolder
R12: 1 kΩ; R_1206_3216Metric_Pad1.30x1.75mm_HandSolder
SW1: SW_SPDT; SW_SPDT_CK_JS102011SAQN
U1: MCP73871-2CC; QFN-20-1EP_4x4mm_P0.5mm_EP2.5x2.5mm
U2: DW01A; SOT-23-6

Connections:
/BAT_NEG: C4.1, J2.2, Q1.1, U2.6 (GND)
/DRAIN_COMMON: Q1.2, Q1.5
/OC: Q1.4, U2.3 (OC)
/OD: Q1.6, U2.1 (OD)
/PG: J5.1, R7.1, U1.6 (~PG)
/STAT1/LBO: J5.2, R8.1, U1.8 (STAT1/~LBO)
/STAT2: J5.3, R9.1, U1.7 (STAT2)
/SYS: C3.1, SW1.2 (B), U1.1 (OUT), U1.20 (OUT)
/SYS_OUT: J3.1, SW1.3 (C)
/THERM: J4.1, JP1.1 (A), U1.5 (THERM)
/VBAT: C2.1, J2.1, J5.5, R11.1, U1.14 (V_{BAT}), U1.15 (V_{BAT}), U1.16 (V_{BAT_SENSE})
/VBUS: C1.2, D1.1 (K), J1.A4 (VBUS), J1.A9 (VBUS), J1.B4 (VBUS), J1.B9 (VBUS), LED1.2 (A), LED2.2 (A), LED3.2 (A), R3.2, U1.4 (PROG2), U1.17 (CE), U1.18 (IN), U1.19 (IN)
GND: C1.1, C2.2, C3.2, D1.2 (A), J1.A1 (GND), J1.A12 (GND), J1.B1 (GND), J1.B12 (GND), J1.SH (SHIELD), J3.2, J4.2, J5.4, Q1.3, R1.1, R2.1, R4.2, R5.2, R6.2, R10.2, R12.2, U1.3 (SEL), U1.9 (~TE), U1.10 (V_{SS}), U1.11 (V_{SS}), U1.21 (V_{SS})
unnamed: J1.A5 (CC1), R2.2
unnamed: J1.B5 (CC2), R1.2
unnamed: JP1.2 (B), R10.1
unnamed: LED1.1 (K), R7.2
unnamed: LED2.1 (K), R8.2
unnamed: LED3.1 (K), R9.2
unnamed: R5.1, U1.13 (PROG1)
unnamed: R6.1, U1.12 (PROG3)
unnamed: R3.1, R4.1, U1.2 (VPCC)
unnamed: R12.1, U2.2 (CS)
unnamed: C4.2, R11.2, U2.5 (VCC)

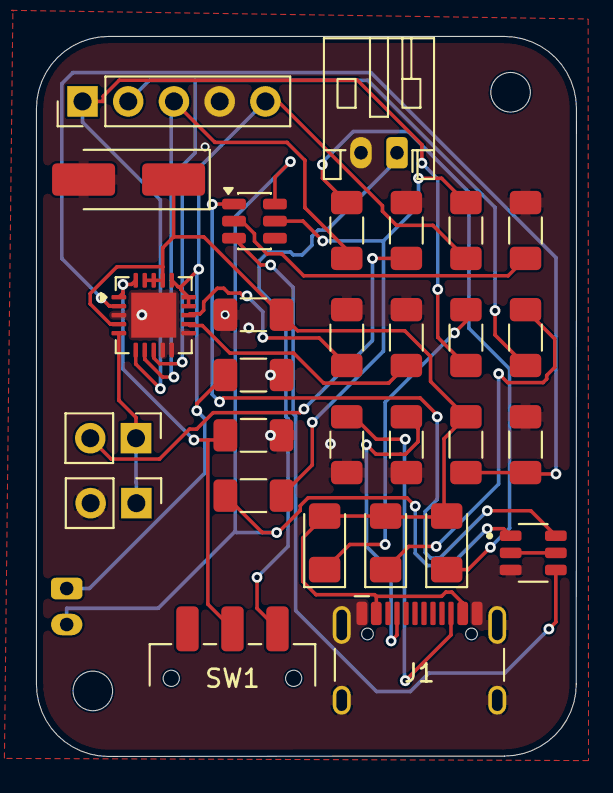
[picture p78: board revisions/2026-09-11_cleanup/KK_power_module/KK_power_module.kicad_pcb from above]

Board: 2 copper layers, 30.0 x 40.0 mm, 32 parts (1 on the bottom side), 24 nets.

Other parts of the board:
H1, H2: MountingHole_2.2mm_M2
